ewfefrs/pi-gaze/hardware/enclosure/clamp_detail.png

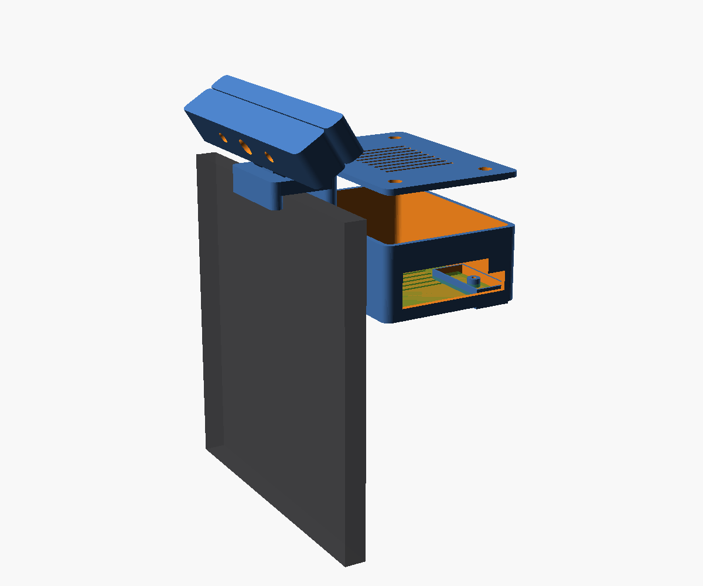
hardware/enclosure/clamp_detail.png
