ewfefrs/pi-gaze/hardware/enclosure/insp_box_in.png

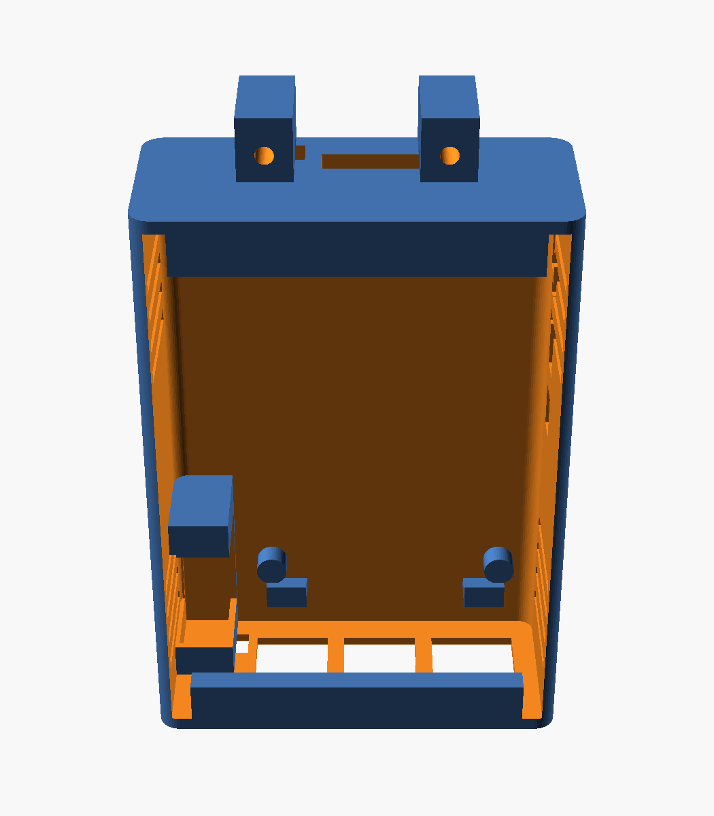
hardware/enclosure/insp_box_in.png
