ewfefrs/pi-gaze/hardware/enclosure/insp_box_xside.png

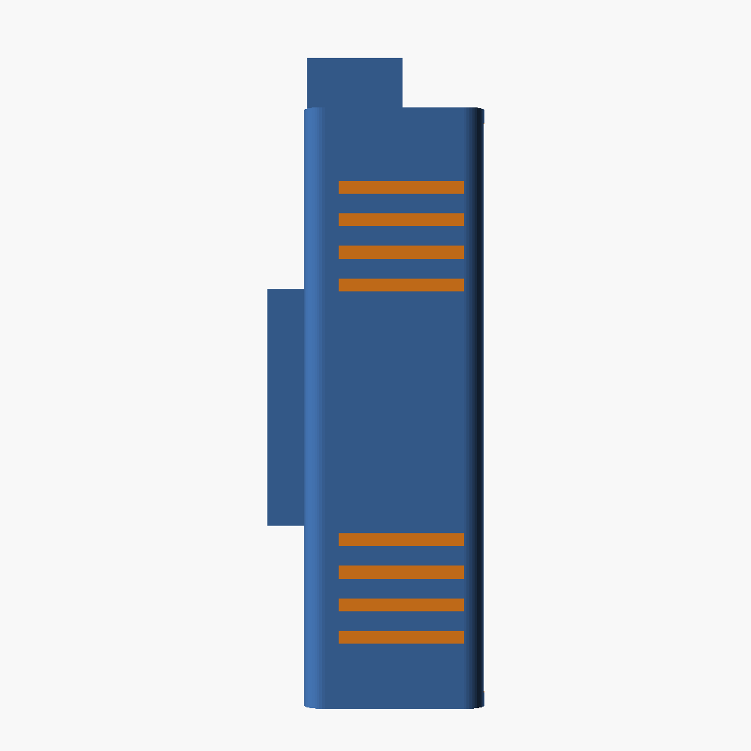
hardware/enclosure/insp_box_xside.png
