ewfefrs/pi-gaze/hardware/enclosure/insp_clamp_back.png

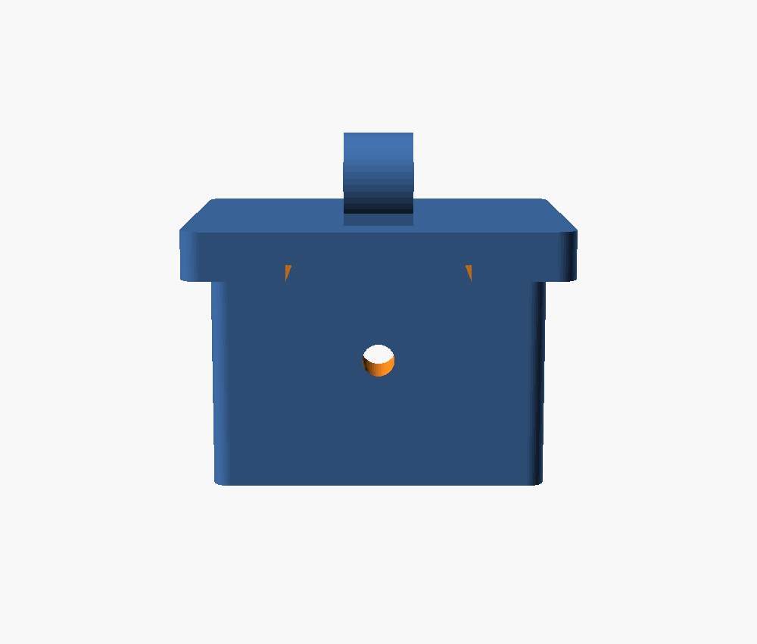
hardware/enclosure/insp_clamp_back.png
