ewfefrs/pi-gaze/hardware/enclosure/out/asm.png

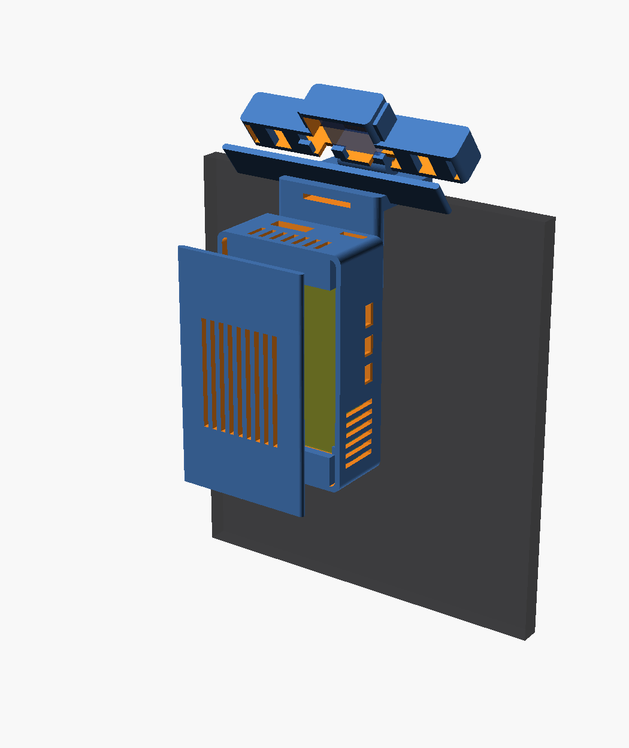
hardware/enclosure/out/asm.png
