ewfefrs/pi-gaze/hardware/enclosure/out/asm_side.png

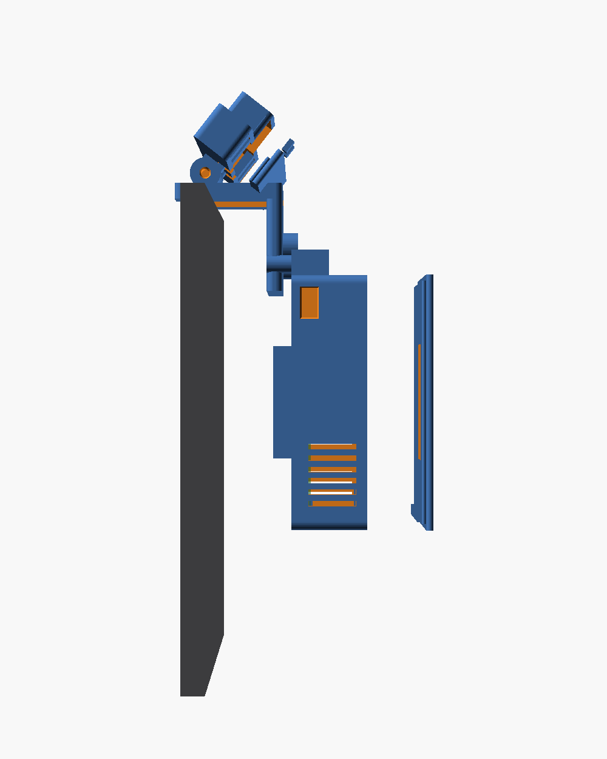
hardware/enclosure/out/asm_side.png
