ewfefrs/pi-gaze/hardware/enclosure/out/bar_back.png

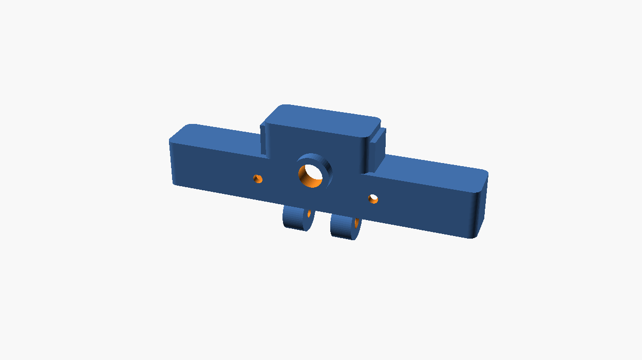
hardware/enclosure/out/bar_back.png
