ewfefrs/pi-gaze/hardware/enclosure/out/bar_iso.png

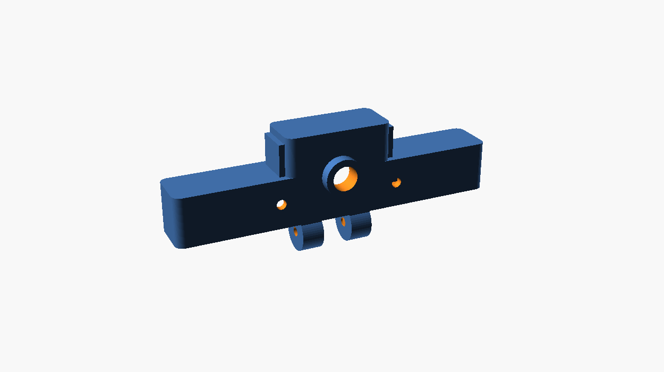
hardware/enclosure/out/bar_iso.png
