ewfefrs/pi-gaze/hardware/enclosure/out/barlid.png

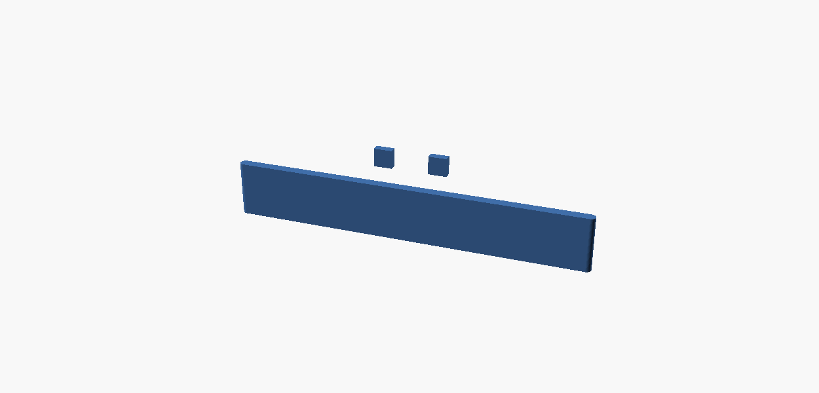
hardware/enclosure/out/barlid.png
