ewfefrs/pi-gaze/hardware/enclosure/out/box_bottom.png

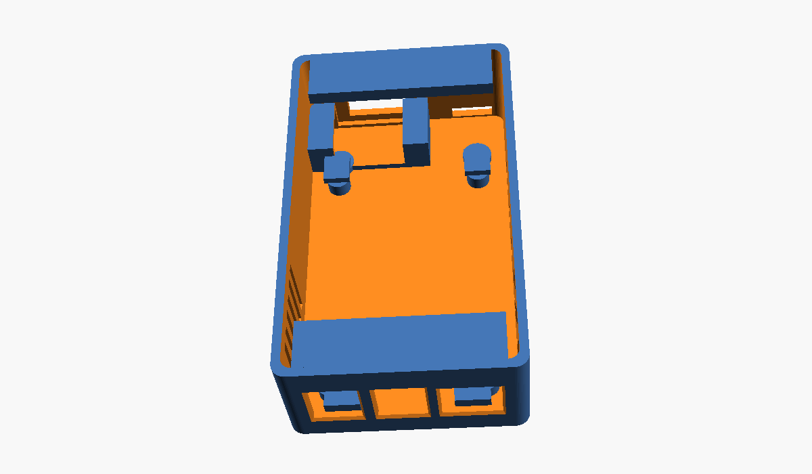
hardware/enclosure/out/box_bottom.png
