ewfefrs/pi-gaze/hardware/enclosure/out/box_ext.png

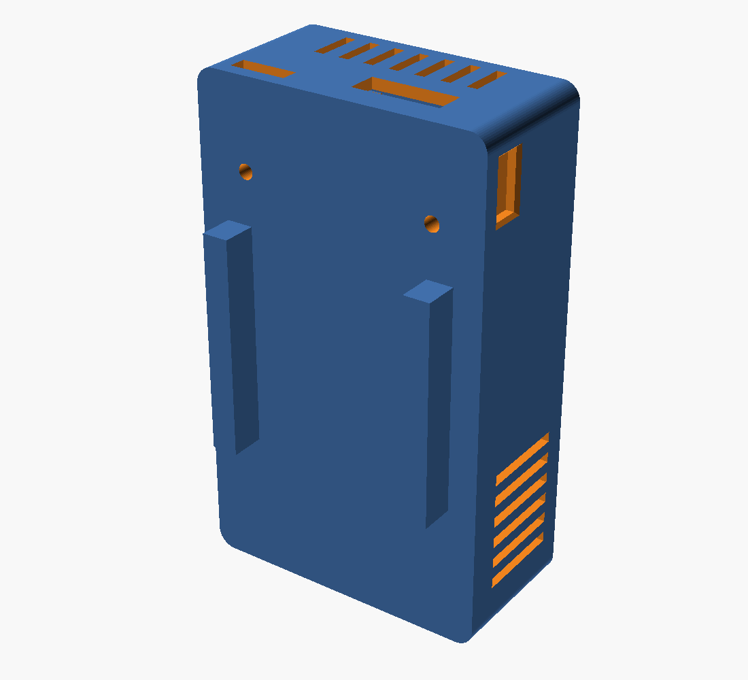
hardware/enclosure/out/box_ext.png
