ewfefrs/pi-gaze/hardware/enclosure/out/box_front.png

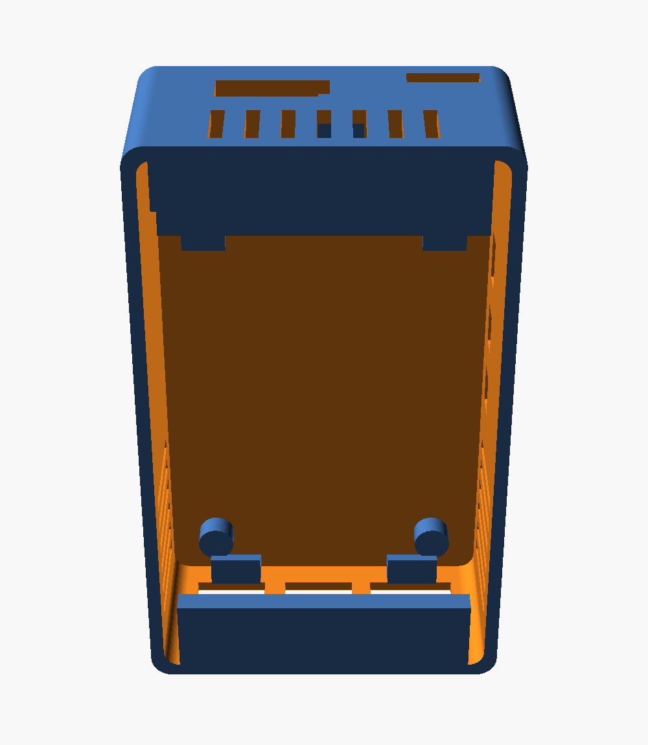
hardware/enclosure/out/box_front.png
