ewfefrs/pi-gaze/hardware/enclosure/out/box_left.png

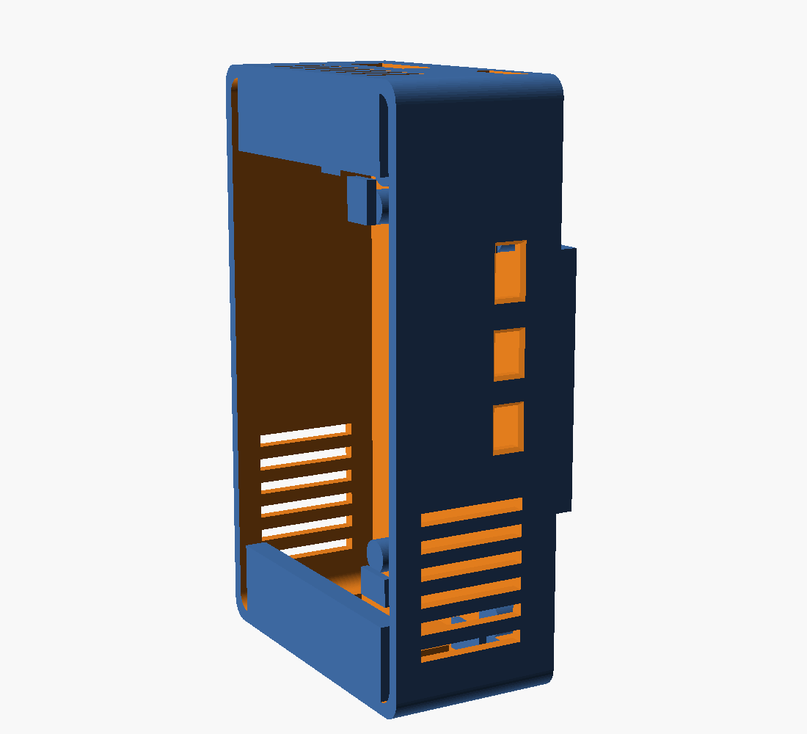
hardware/enclosure/out/box_left.png
