ewfefrs/pi-gaze/hardware/enclosure/out/box_top.png

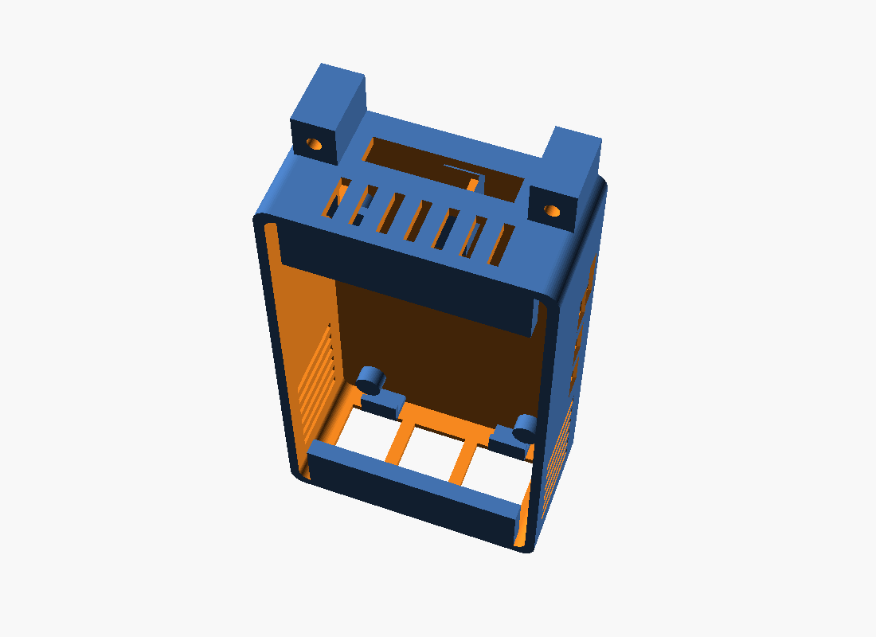
hardware/enclosure/out/box_top.png
