ewfefrs/pi-gaze/hardware/enclosure/out/chk_knob.png

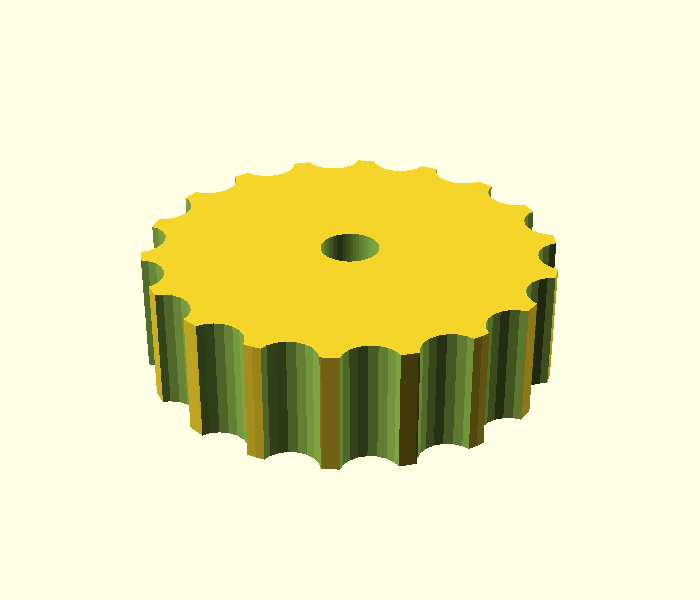
hardware/enclosure/out/chk_knob.png
