ewfefrs/pi-gaze/hardware/enclosure/out/clamp_iso.png

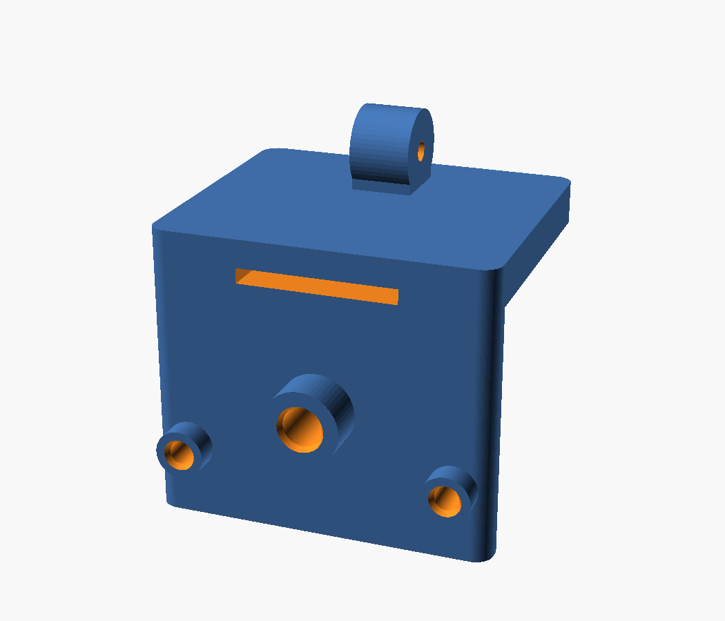
hardware/enclosure/out/clamp_iso.png
