ewfefrs/pi-gaze/hardware/enclosure/out/face_bottom.png

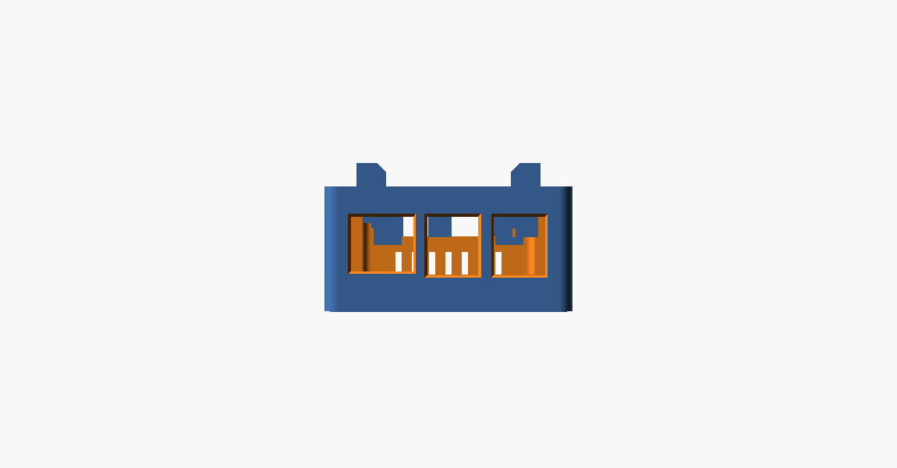
hardware/enclosure/out/face_bottom.png
