ewfefrs/pi-gaze/hardware/enclosure/out/face_left.png

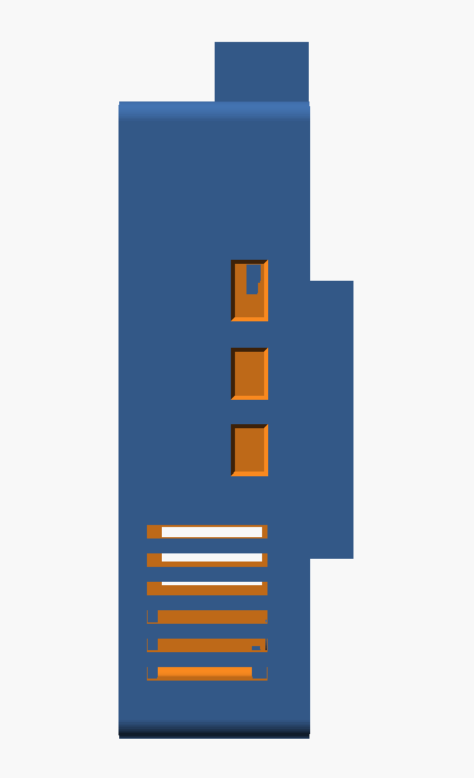
hardware/enclosure/out/face_left.png
