ewfefrs/pi-gaze/hardware/enclosure/out/face_top.png

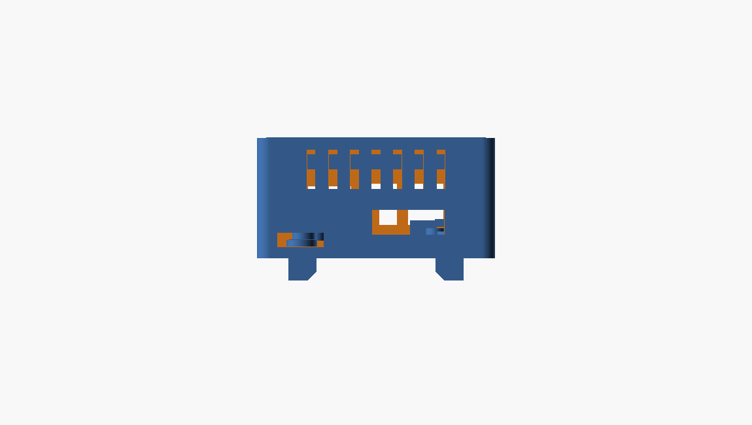
hardware/enclosure/out/face_top.png
