ewfefrs/pi-gaze/hardware/enclosure/out/final_asm2.png

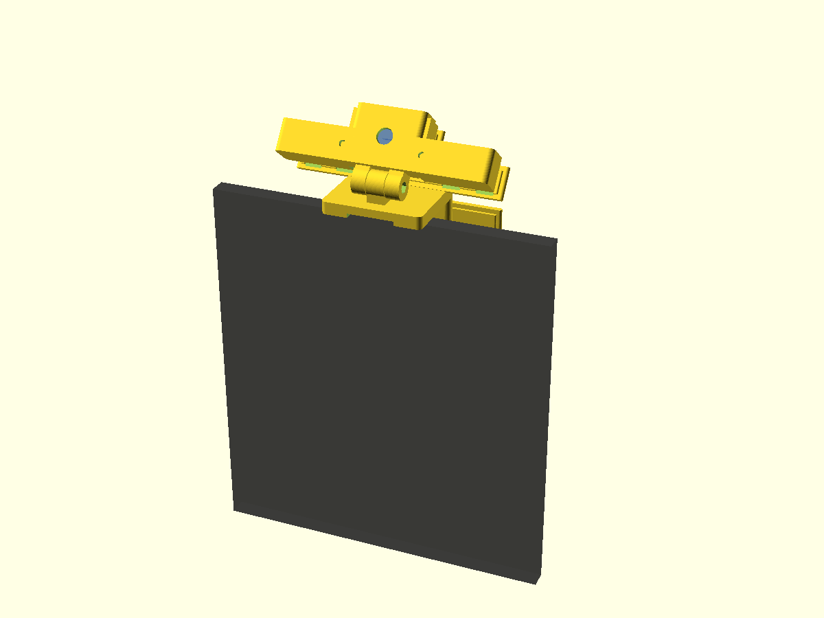
hardware/enclosure/out/final_asm2.png
