ewfefrs/pi-gaze/hardware/enclosure/out/final_barlid.png

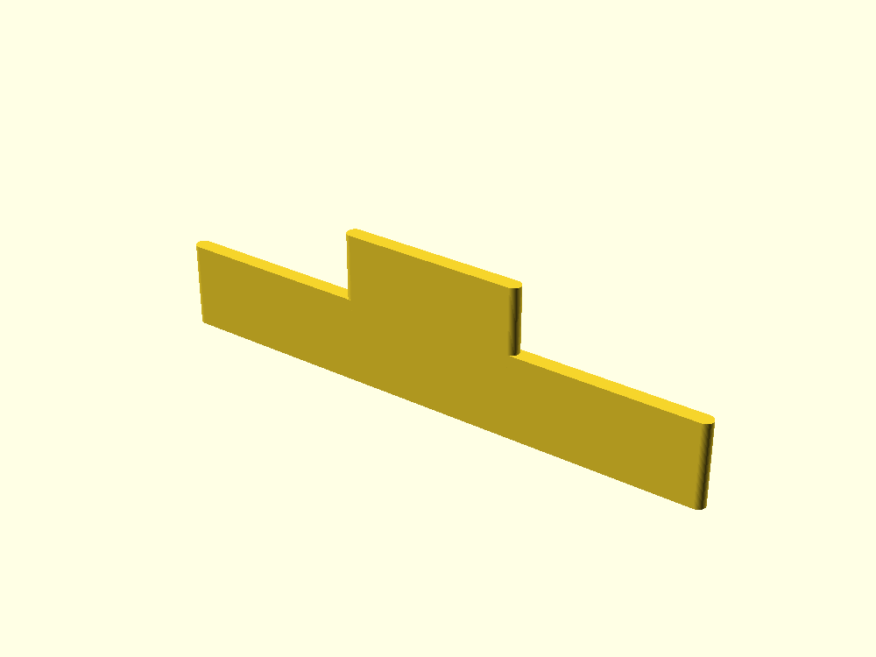
hardware/enclosure/out/final_barlid.png
