ewfefrs/pi-gaze/hardware/enclosure/out/final_box_back.png

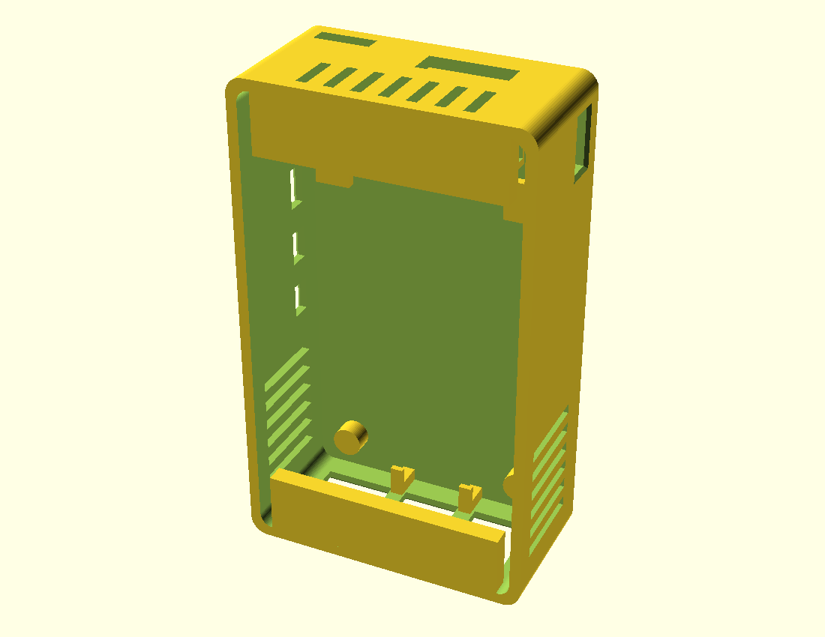
hardware/enclosure/out/final_box_back.png
