ewfefrs/pi-gaze/hardware/enclosure/out/final_box_cut.png

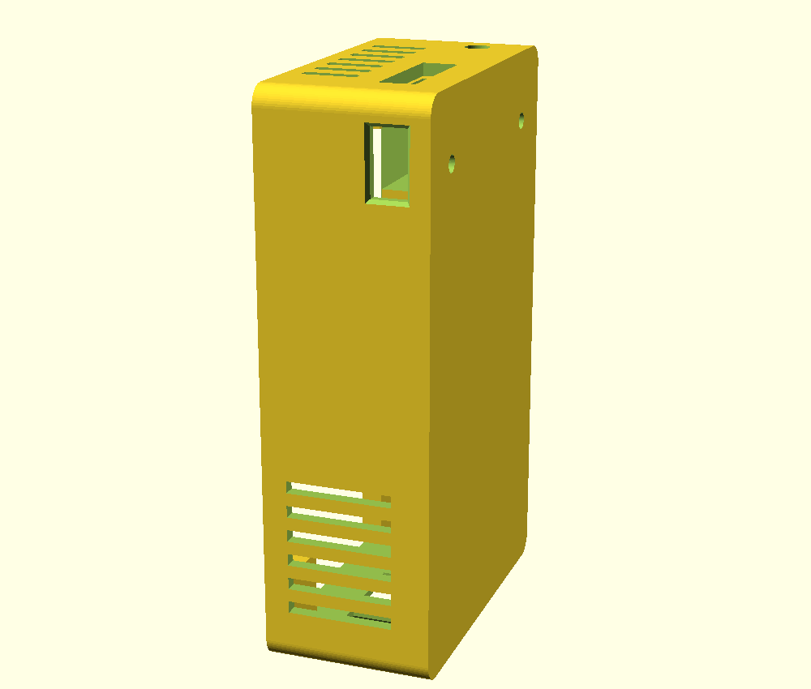
hardware/enclosure/out/final_box_cut.png
