ewfefrs/pi-gaze/hardware/enclosure/out/final_box_ports.png

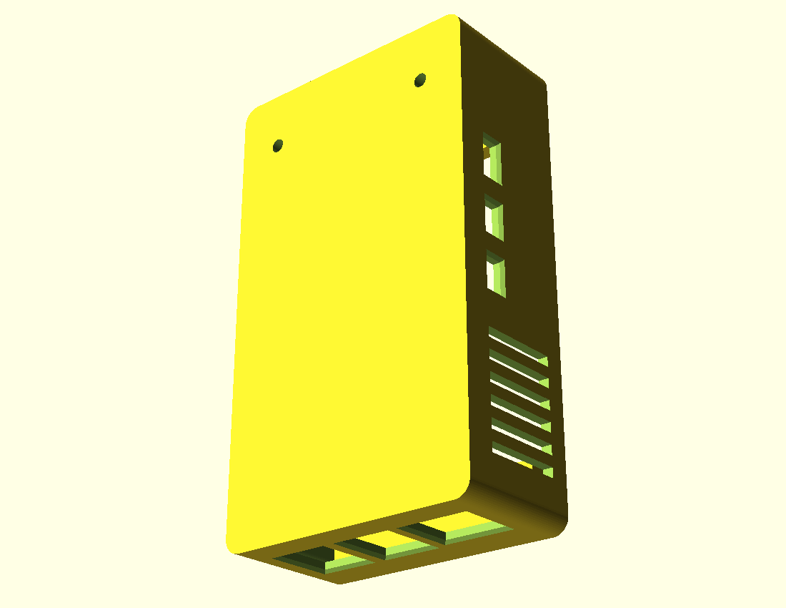
hardware/enclosure/out/final_box_ports.png
