ewfefrs/pi-gaze/hardware/enclosure/out/final_box_pwr.png

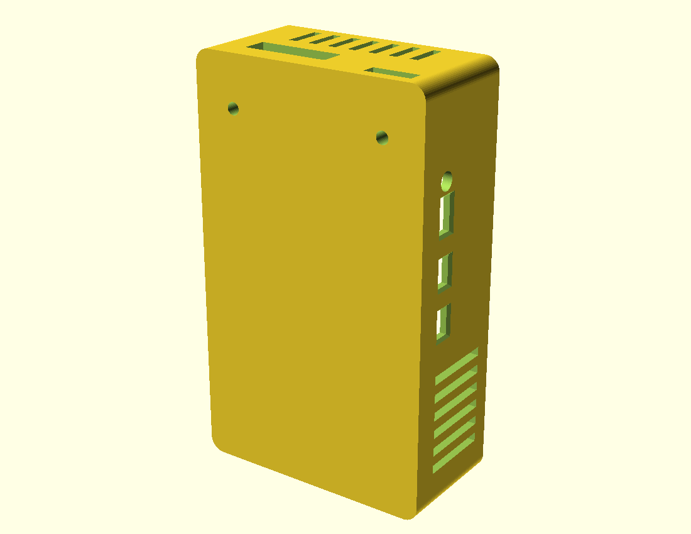
hardware/enclosure/out/final_box_pwr.png
