ewfefrs/pi-gaze/hardware/enclosure/out/final_box_top.png

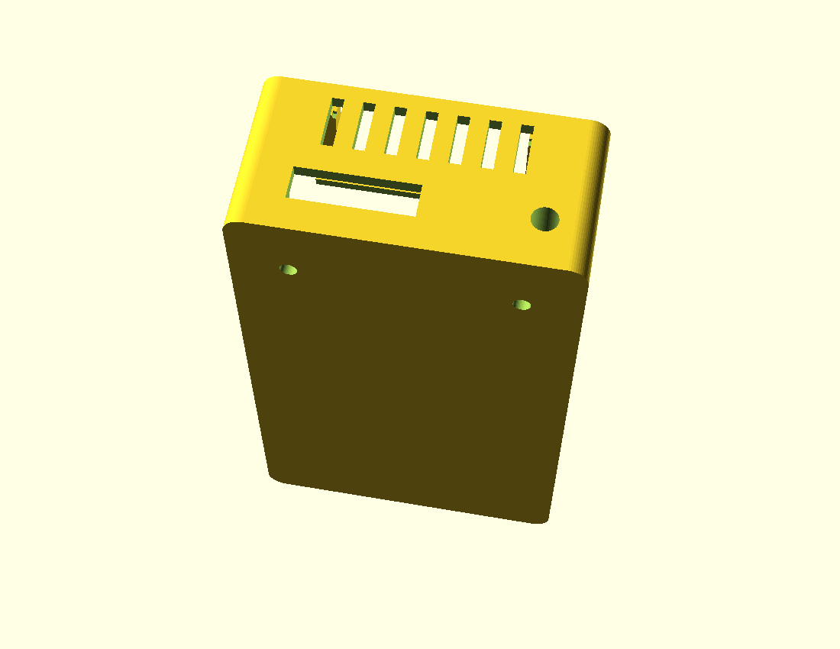
hardware/enclosure/out/final_box_top.png
