ewfefrs/pi-gaze/hardware/enclosure/out/final_clamp.png

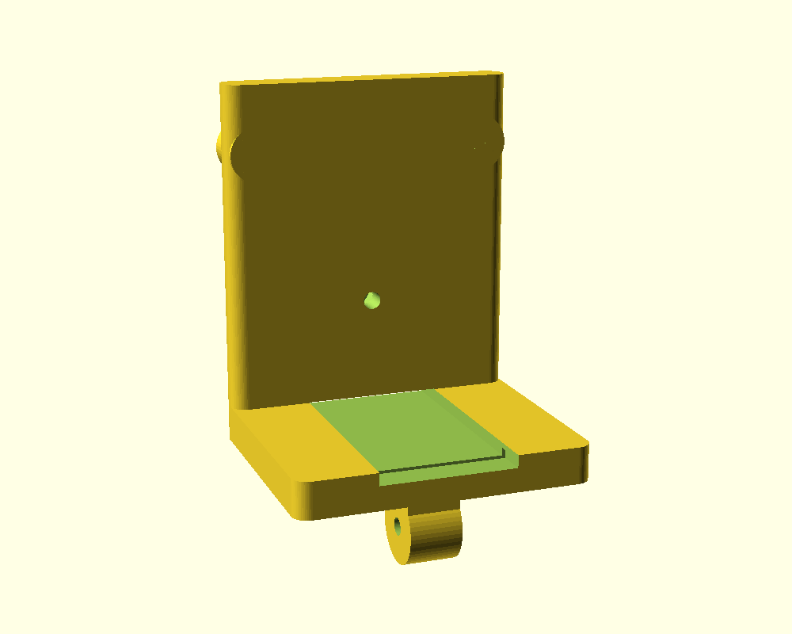
hardware/enclosure/out/final_clamp.png
