ewfefrs/pi-gaze/hardware/enclosure/out/foot_back.png

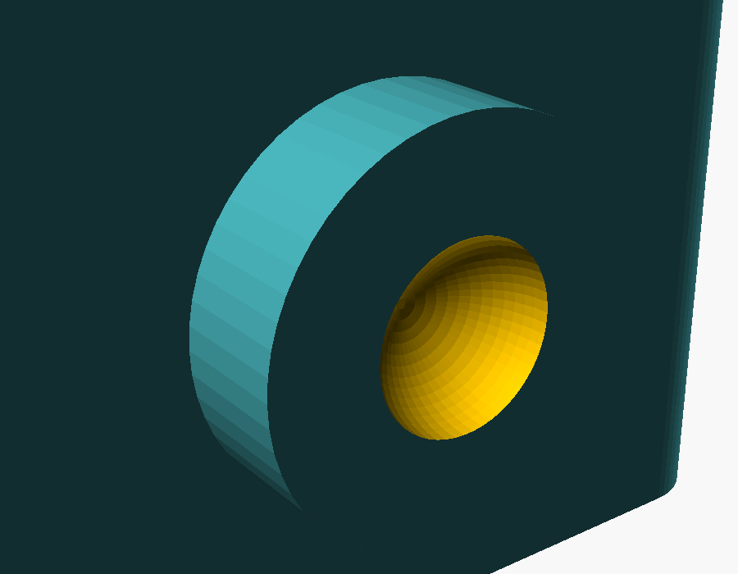
hardware/enclosure/out/foot_back.png
