ewfefrs/pi-gaze/hardware/enclosure/out/foot_fixed.png

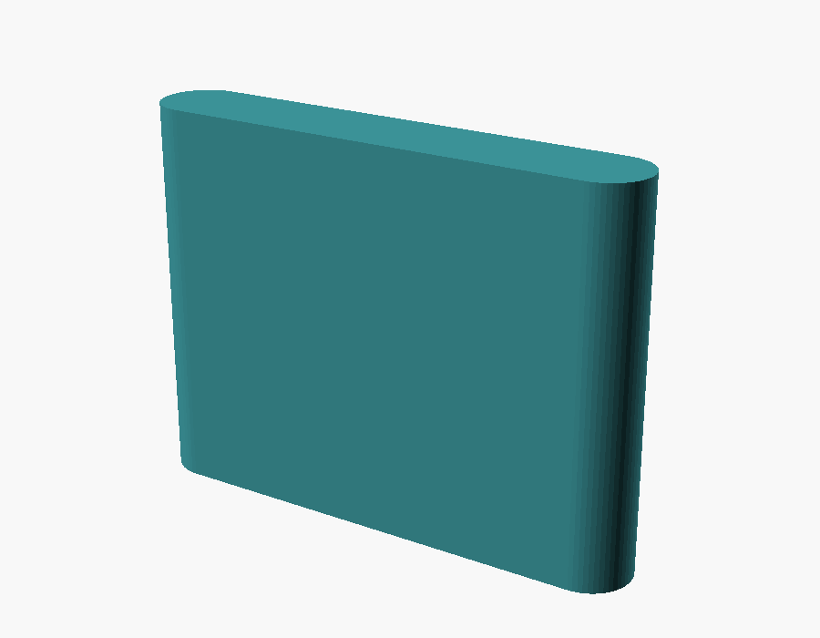
hardware/enclosure/out/foot_fixed.png
