ewfefrs/pi-gaze/hardware/enclosure/out/id_bar_lid.png

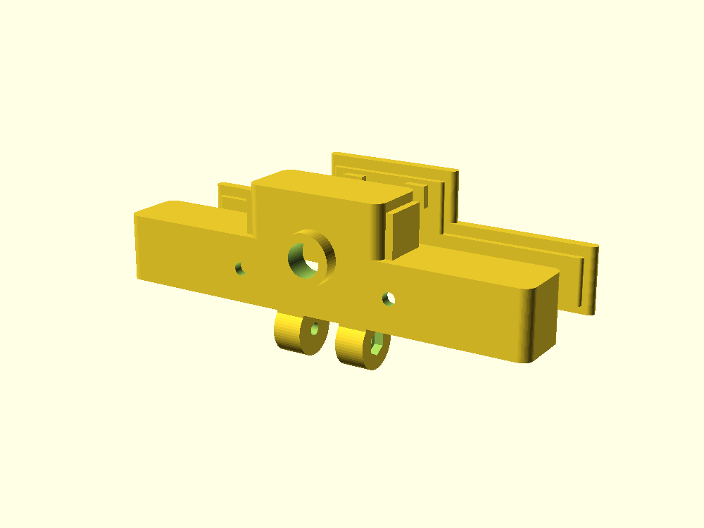
hardware/enclosure/out/id_bar_lid.png
