ewfefrs/pi-gaze/hardware/enclosure/out/id_box_front.png

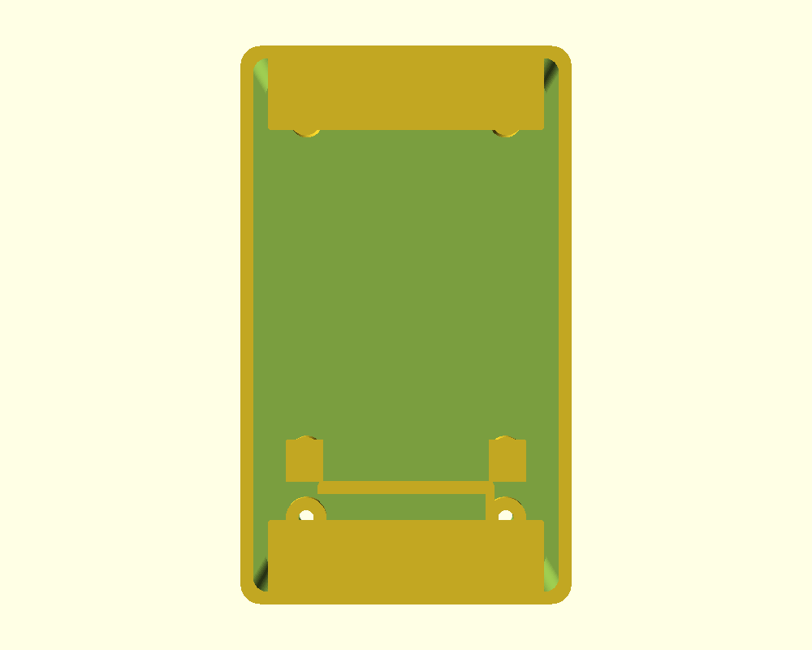
hardware/enclosure/out/id_box_front.png
