ewfefrs/pi-gaze/hardware/enclosure/out/id_clamp_under.png

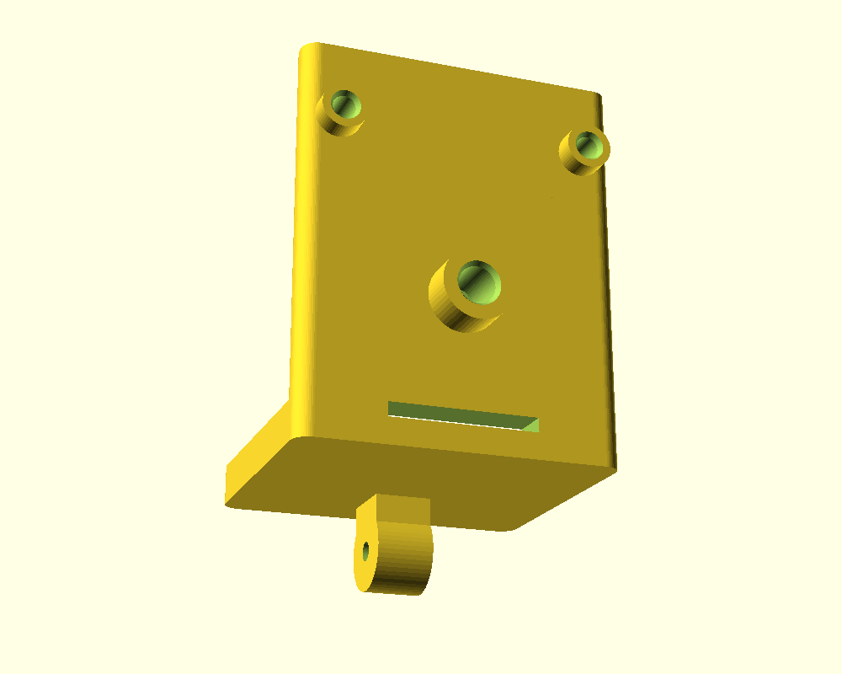
hardware/enclosure/out/id_clamp_under.png
