ewfefrs/pi-gaze/hardware/enclosure/out/insp_asm.png

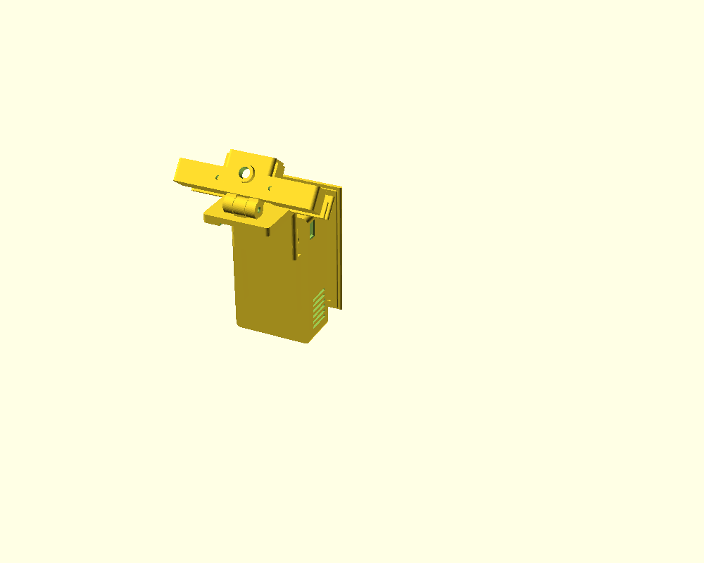
hardware/enclosure/out/insp_asm.png
