ewfefrs/pi-gaze/hardware/enclosure/out/insp_hinge.png

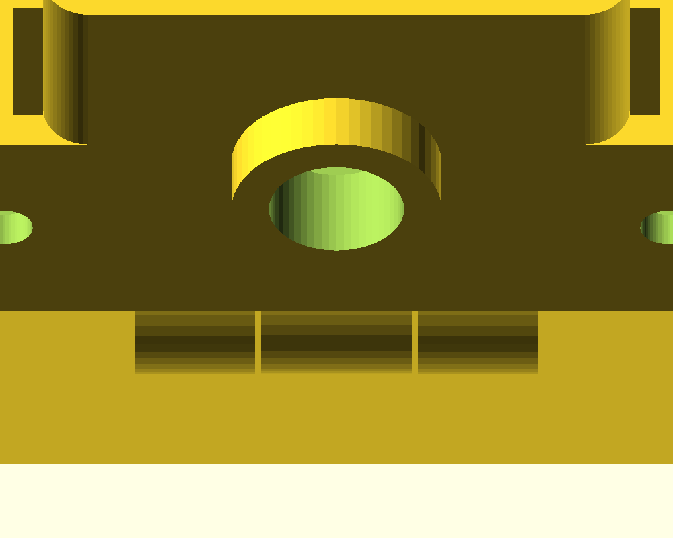
hardware/enclosure/out/insp_hinge.png
