ewfefrs/pi-gaze/hardware/enclosure/out/lid.png

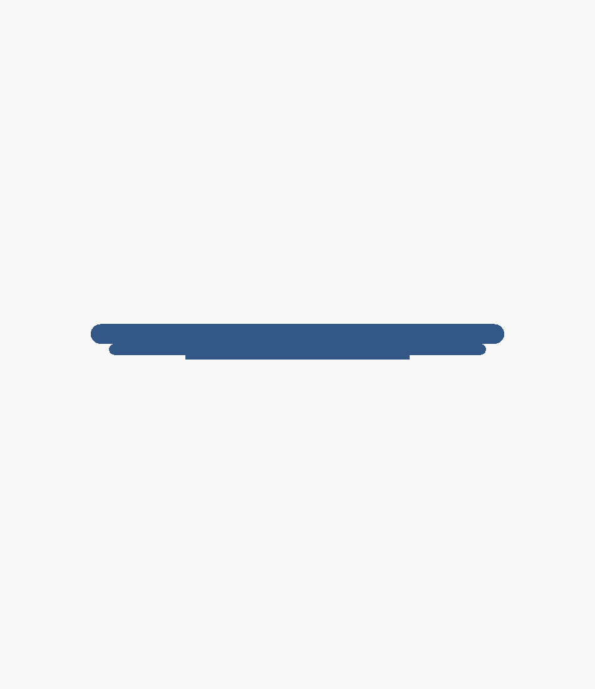
hardware/enclosure/out/lid.png
