ewfefrs/pi-gaze/hardware/enclosure/out/lid_back.png

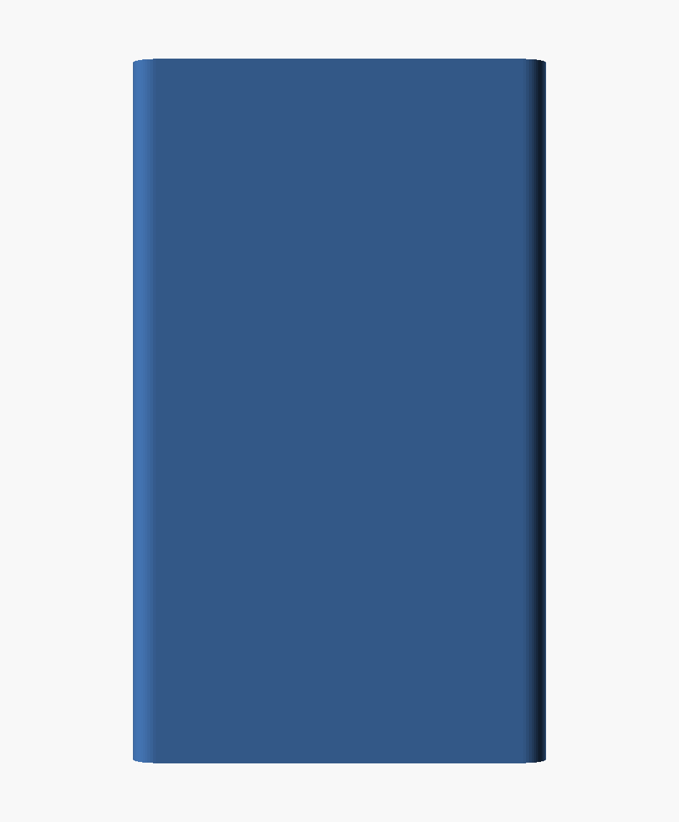
hardware/enclosure/out/lid_back.png
