ewfefrs/pi-gaze/hardware/enclosure/out/lid_iso.png

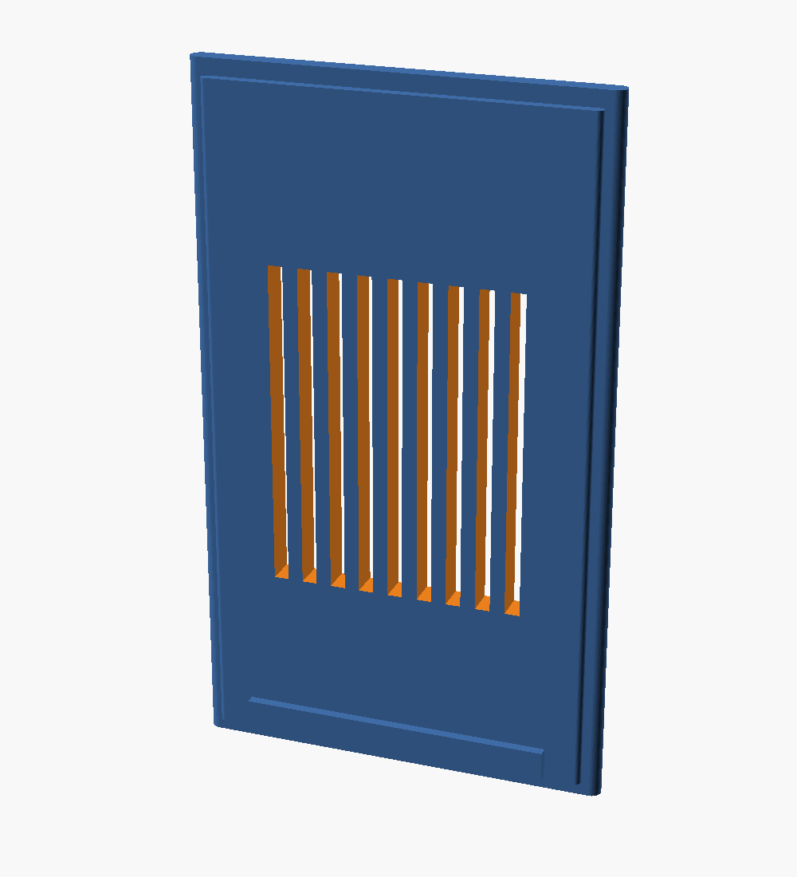
hardware/enclosure/out/lid_iso.png
