ewfefrs/pi-gaze/hardware/enclosure/out/oh_bar_front.png

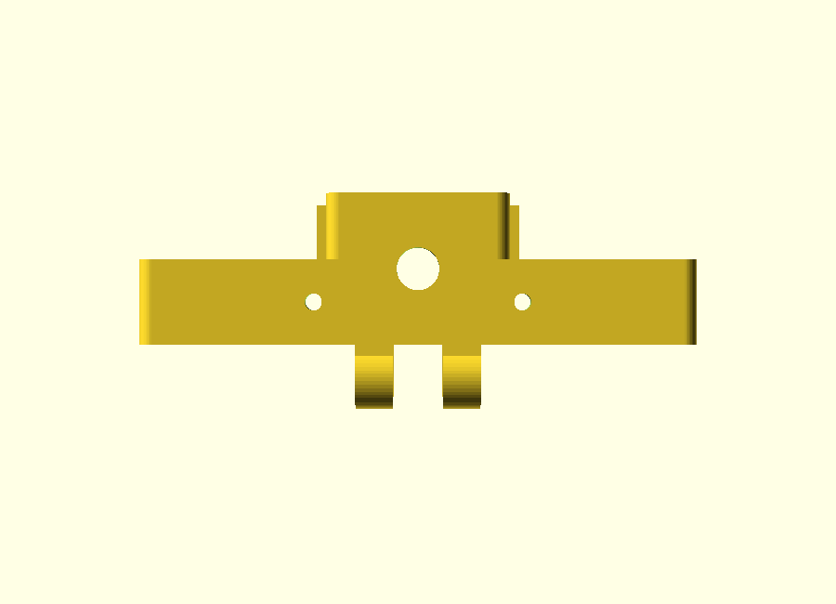
hardware/enclosure/out/oh_bar_front.png
