ewfefrs/pi-gaze/hardware/enclosure/out/oh_clamp.png

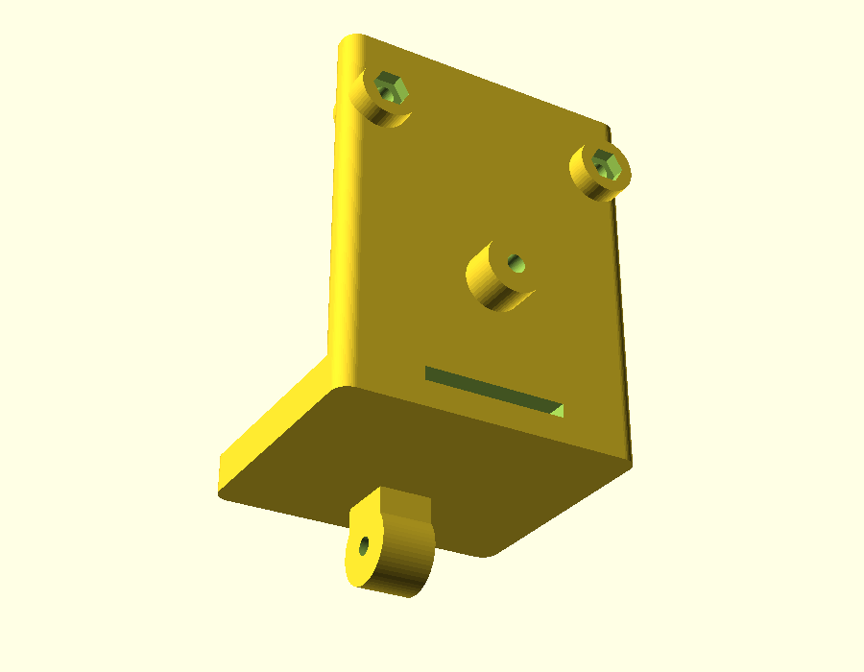
hardware/enclosure/out/oh_clamp.png
