ewfefrs/pi-gaze/hardware/enclosure/out/ov_a.png

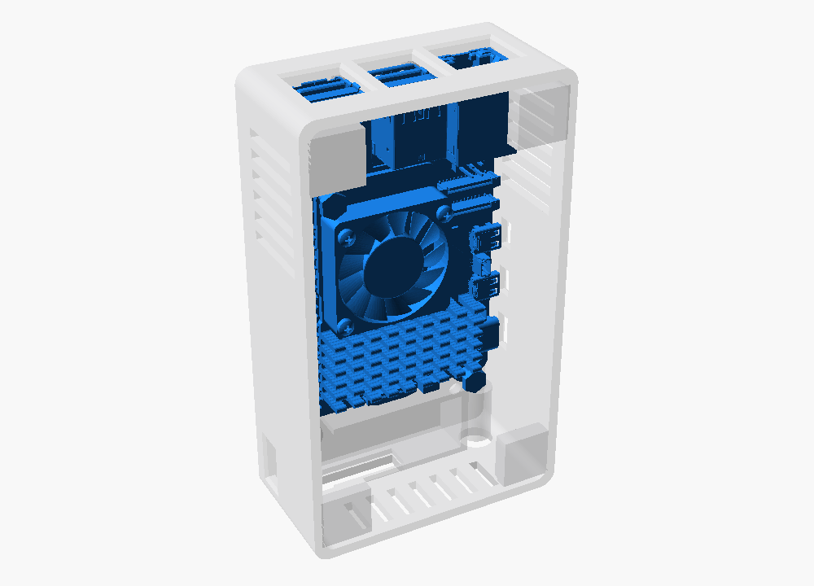
hardware/enclosure/out/ov_a.png
