ewfefrs/pi-gaze/hardware/enclosure/out/ov_side.png

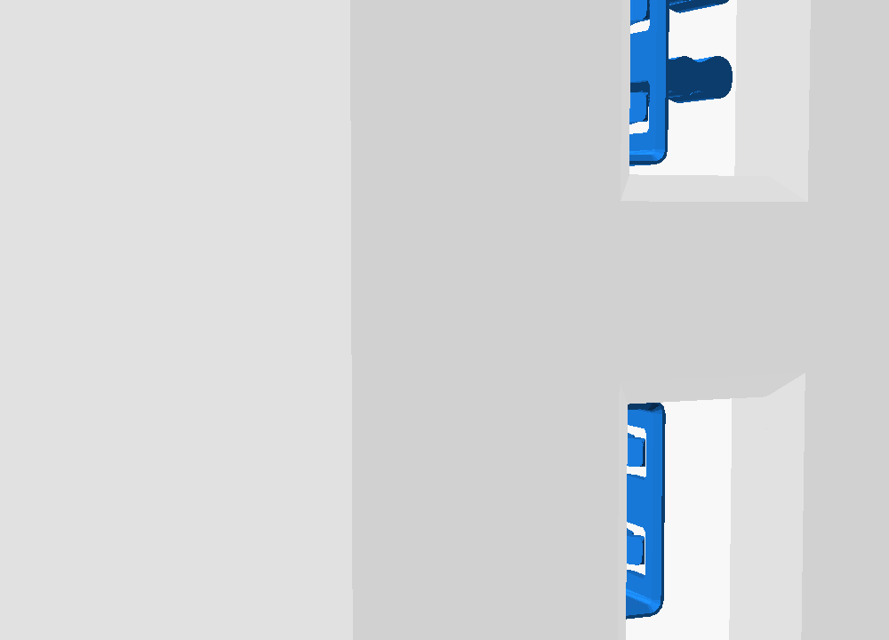
hardware/enclosure/out/ov_side.png
