ewfefrs/pi-gaze/hardware/enclosure/preview_front.png

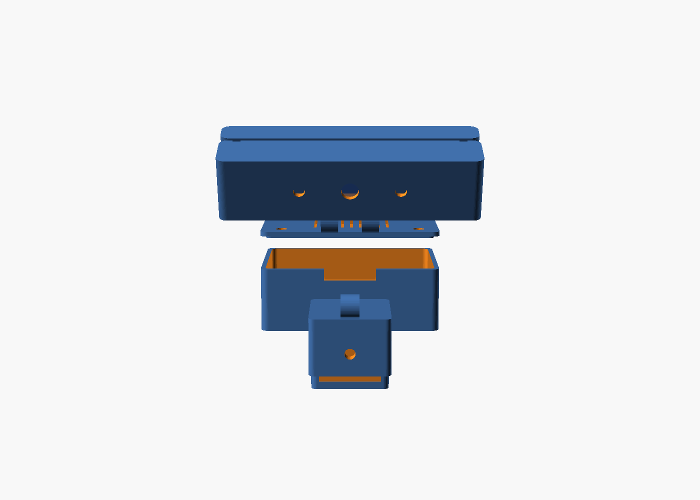
hardware/enclosure/preview_front.png
