ewfefrs/pi-gaze/hardware/enclosure/preview_iso.png

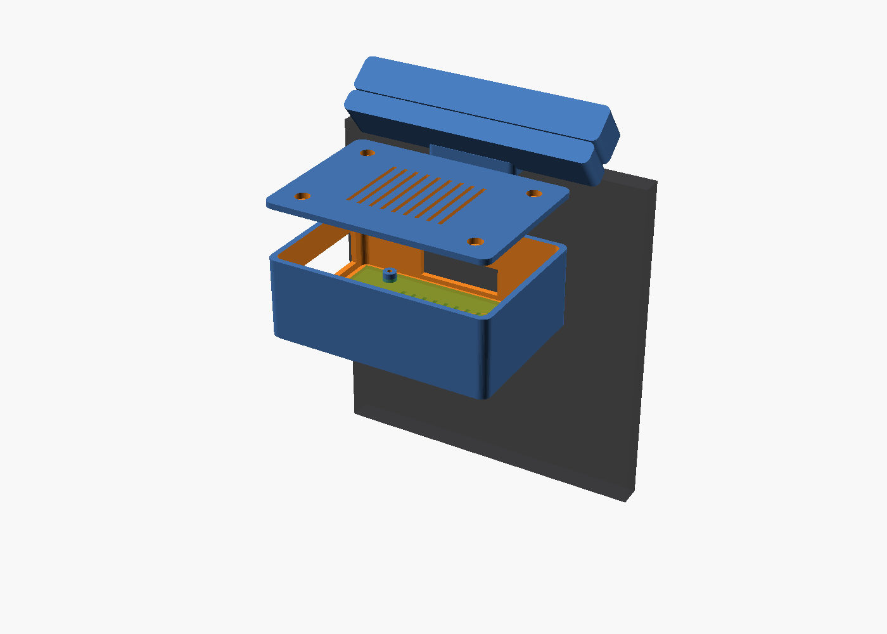
hardware/enclosure/preview_iso.png
