ewfefrs/pi-gaze/hardware/enclosure/preview_side.png

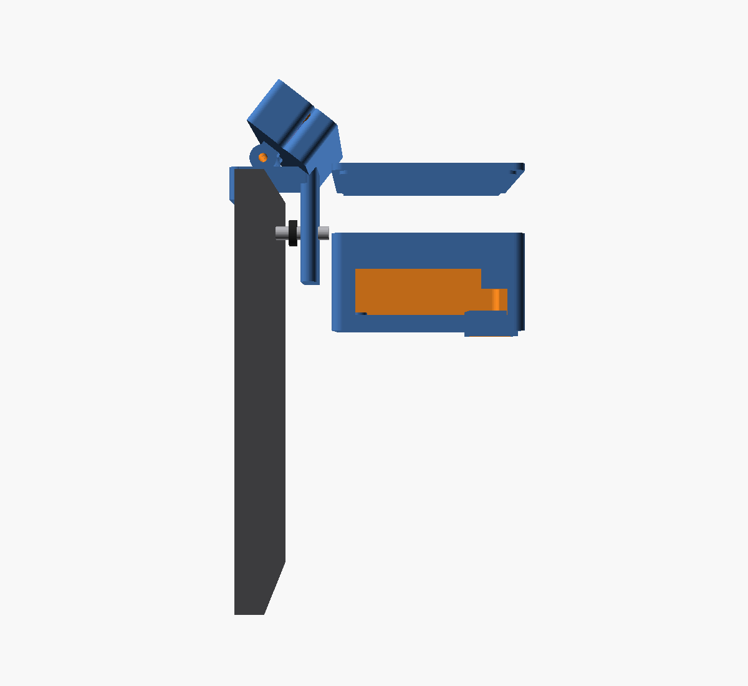
hardware/enclosure/preview_side.png
