ewfefrs/pi-gaze/hardware/enclosure/v3_box.png

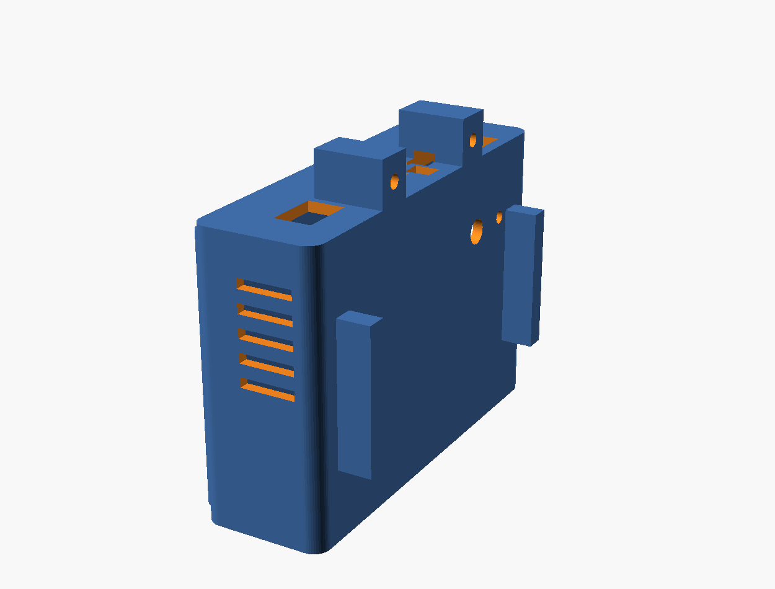
hardware/enclosure/v3_box.png
