ewfefrs/pi-gaze/hardware/enclosure/v3_ports.png

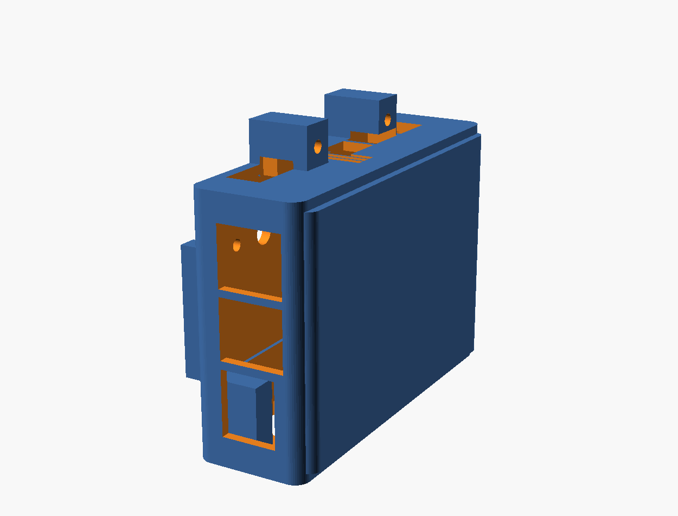
hardware/enclosure/v3_ports.png
