ewfefrs/pi-gaze/hardware/enclosure/v3_side.png

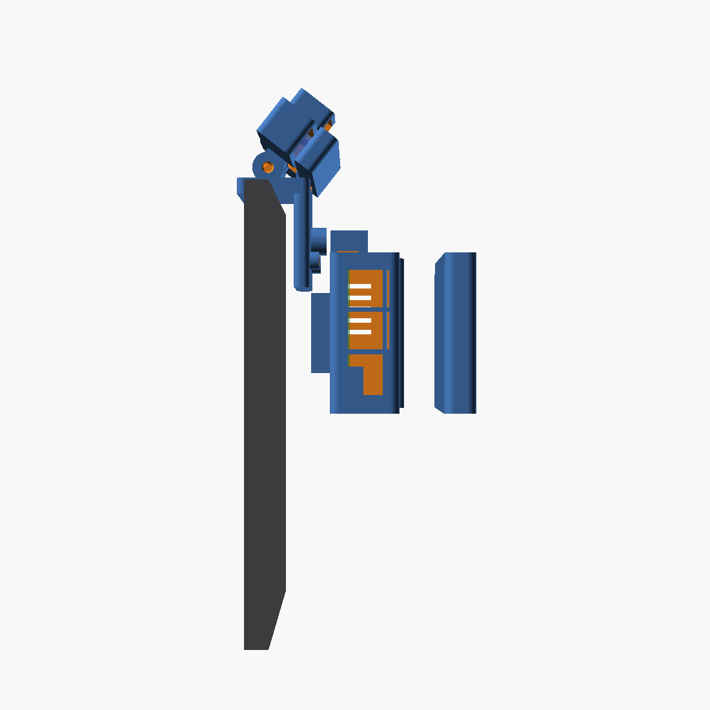
hardware/enclosure/v3_side.png
