ewfefrs/pi-gaze/hardware/enclosure/v4_box.png

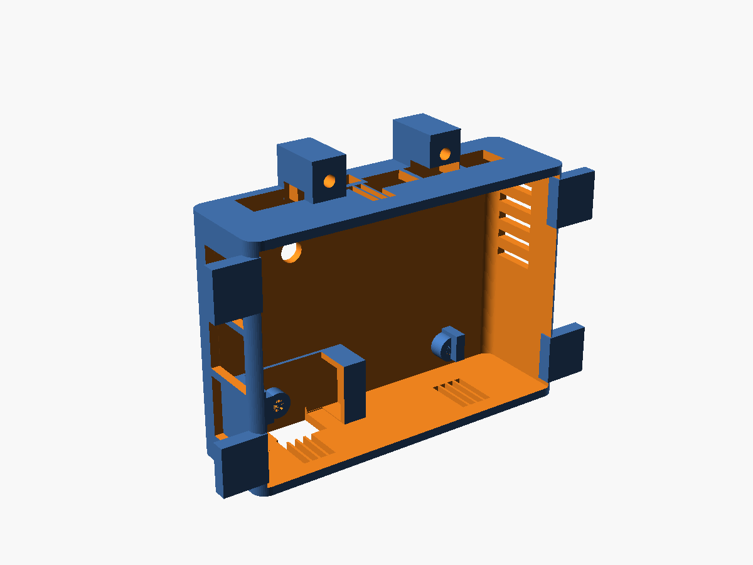
hardware/enclosure/v4_box.png
