ewfefrs/pi-gaze/hardware/enclosure/v5_asm.png

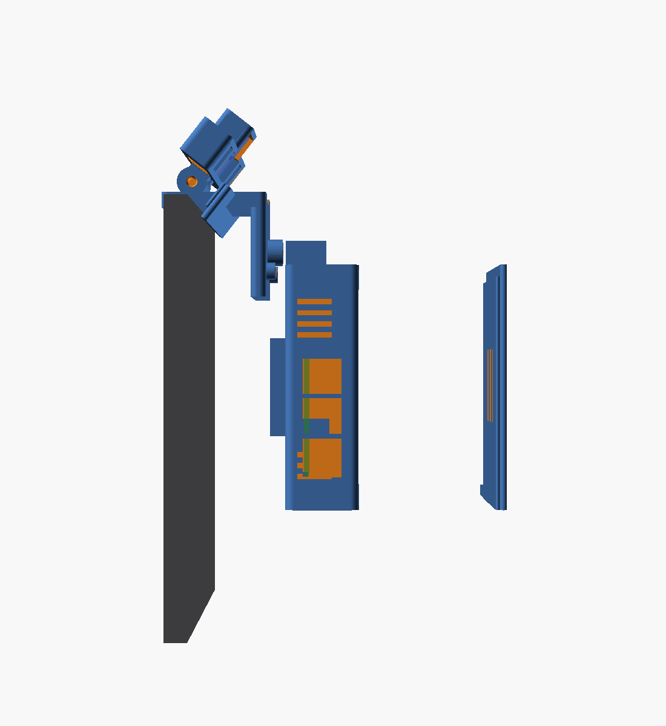
hardware/enclosure/v5_asm.png
