ewfefrs/pi-gaze/hardware/enclosure/v5_barlid.png

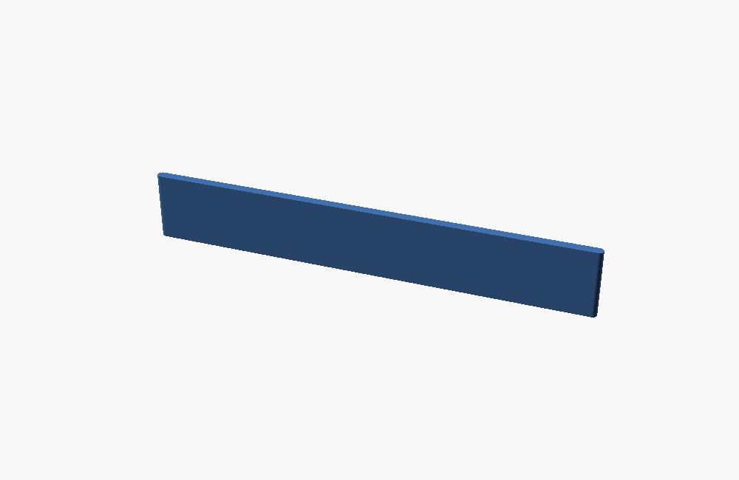
hardware/enclosure/v5_barlid.png
