ewfefrs/pi-gaze/hardware/enclosure/v5_bottom.png

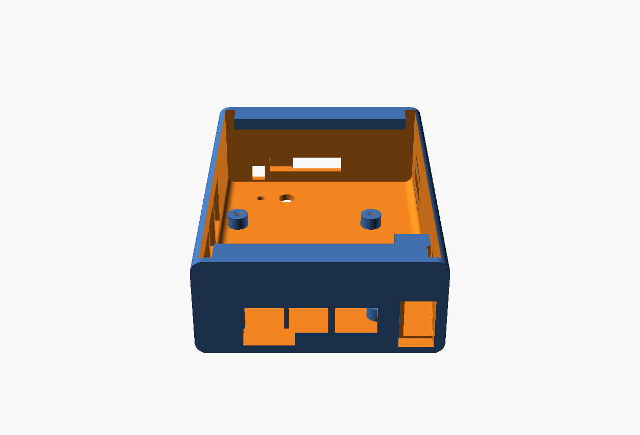
hardware/enclosure/v5_bottom.png
