ewfefrs/pi-gaze/hardware/enclosure/v5_clamp1.png

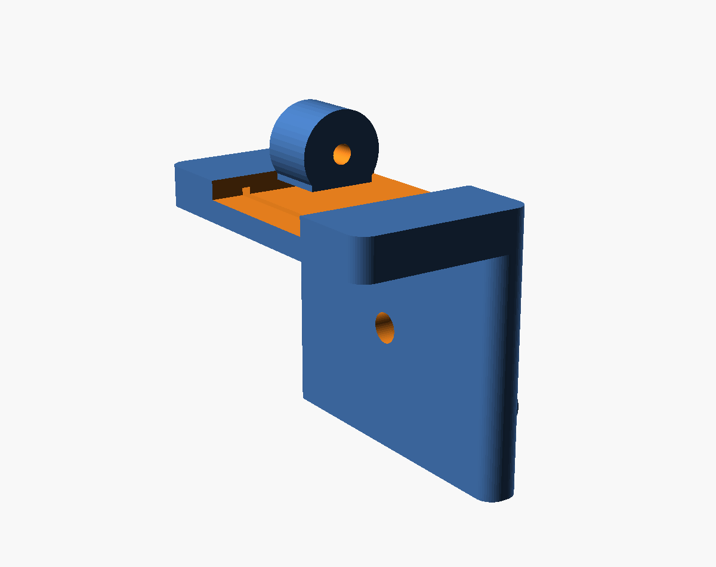
hardware/enclosure/v5_clamp1.png
