ewfefrs/pi-gaze/hardware/enclosure/v5_clamp2.png

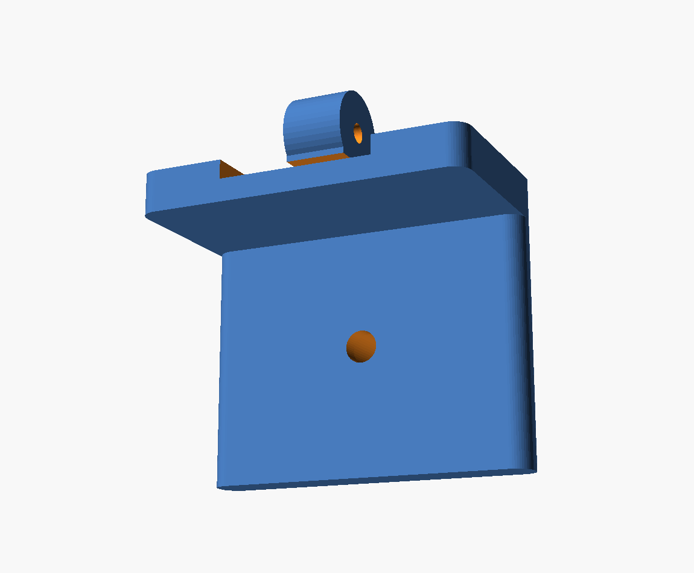
hardware/enclosure/v5_clamp2.png
