ewfefrs/pi-gaze/hardware/enclosure/v5_clamp3.png

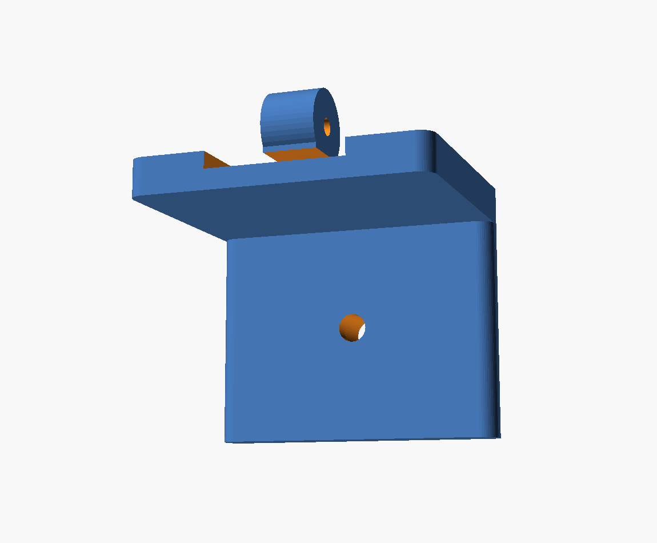
hardware/enclosure/v5_clamp3.png
