ewfefrs/pi-gaze/hardware/enclosure/v5_lid2.png

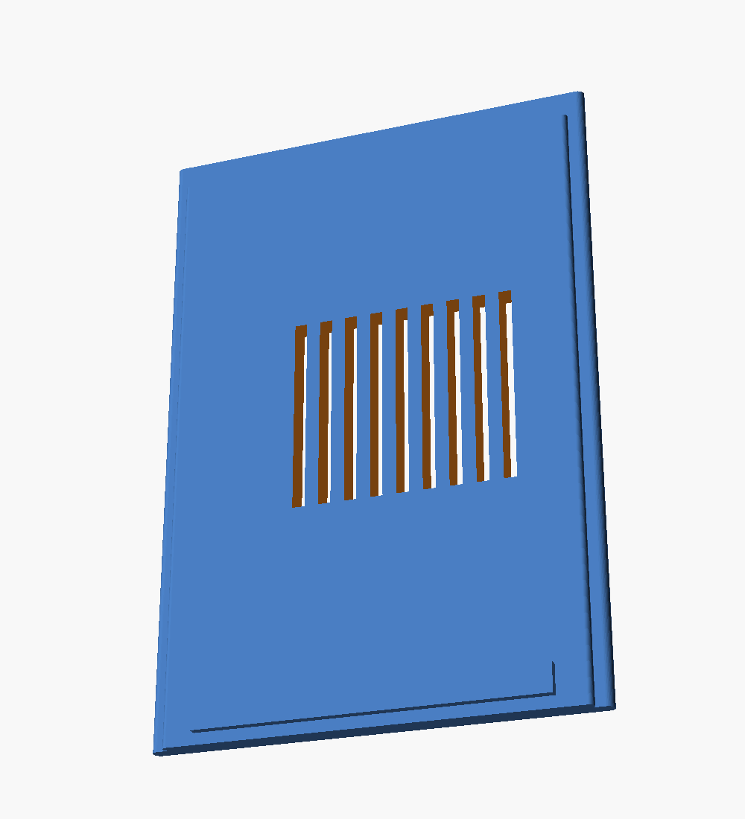
hardware/enclosure/v5_lid2.png
