ewfefrs/pi-gaze/hardware/enclosure/v5_open.png

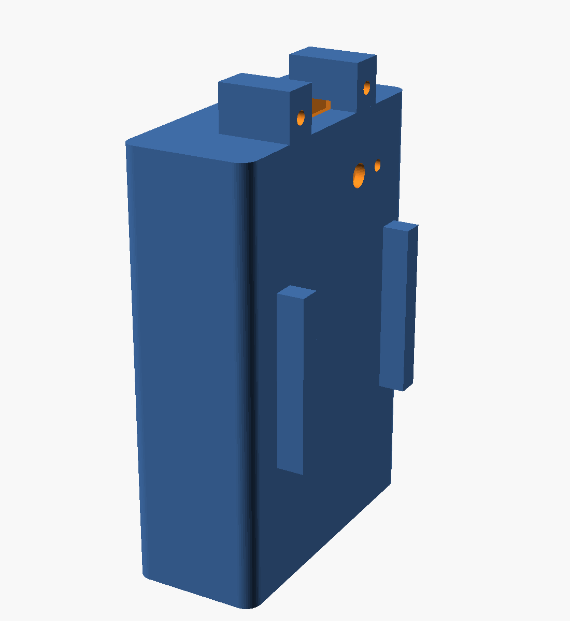
hardware/enclosure/v5_open.png
