ewfefrs/pi-gaze/hardware/enclosure/v5_side.png

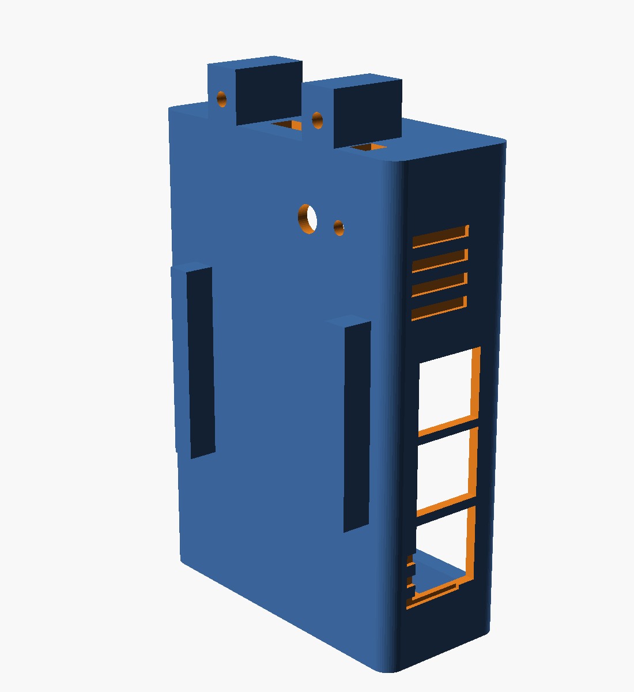
hardware/enclosure/v5_side.png
