ewfefrs/pi-gaze/hardware/enclosure/v6_asm.png

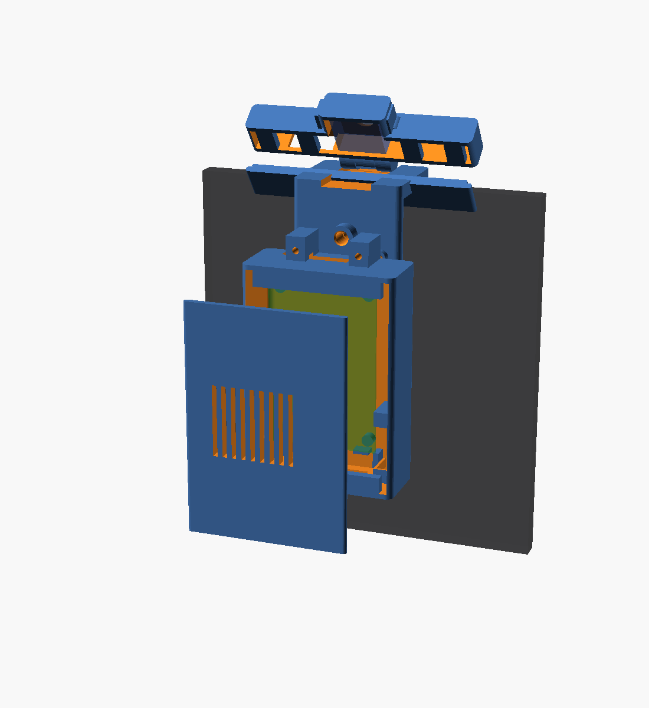
hardware/enclosure/v6_asm.png
