ewfefrs/pi-gaze/hardware/enclosure/v6_front.png

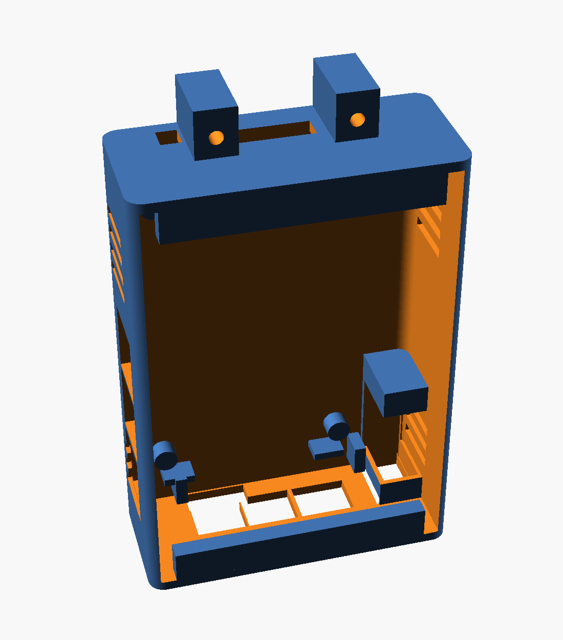
hardware/enclosure/v6_front.png
