ewfefrs/pi-gaze/hardware/enclosure/v6_lid.png

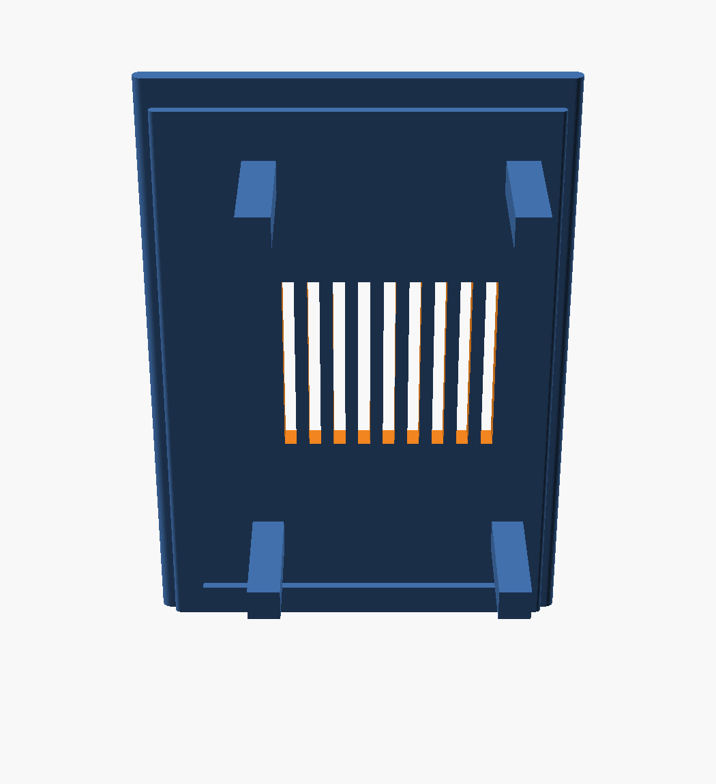
hardware/enclosure/v6_lid.png
