ewfefrs/pi-gaze/hardware/enclosure/v7_bottom.png

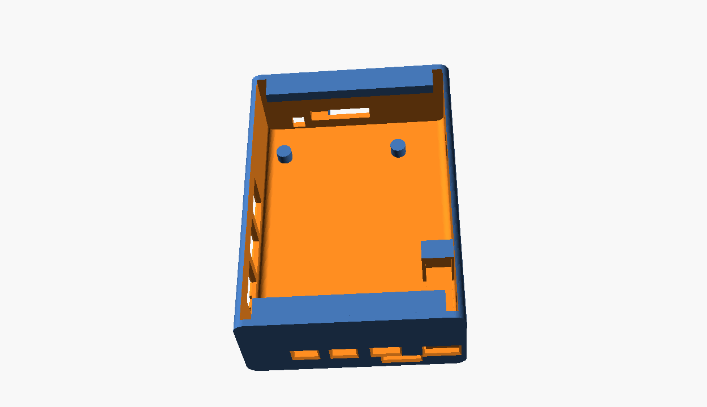
hardware/enclosure/v7_bottom.png
