ewfefrs/pi-gaze/hardware/enclosure/v7_hero.png

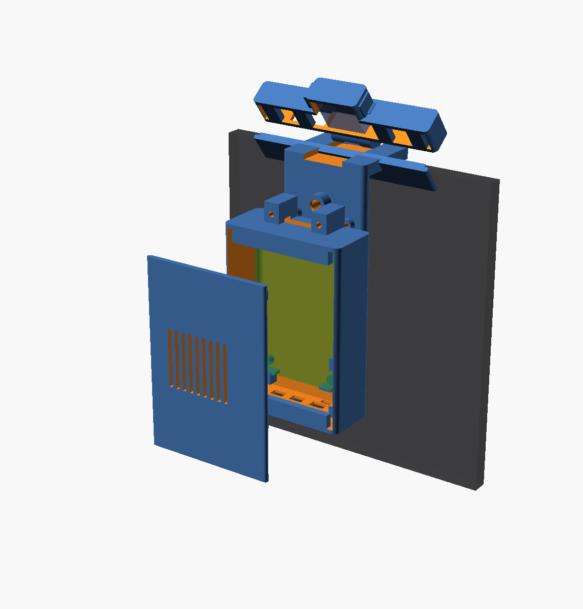
hardware/enclosure/v7_hero.png
