ewfefrs/pi-gaze/hardware/enclosure/v7_side.png

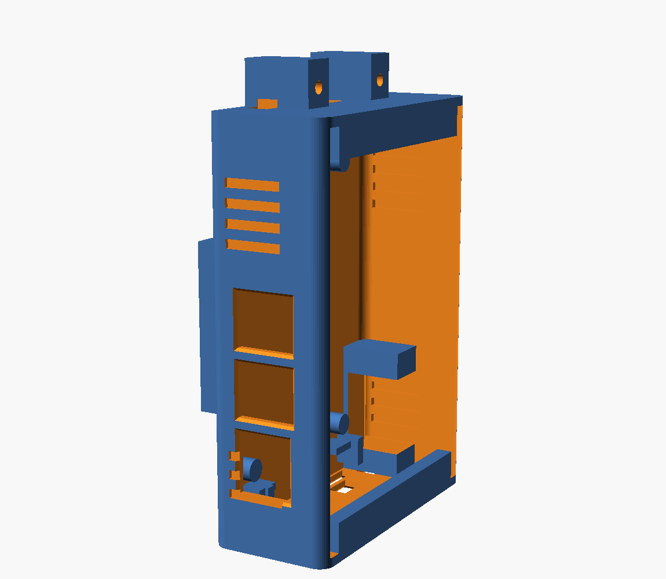
hardware/enclosure/v7_side.png
