ewfefrs/pi-gaze/hardware/enclosure/v8_bottom.png

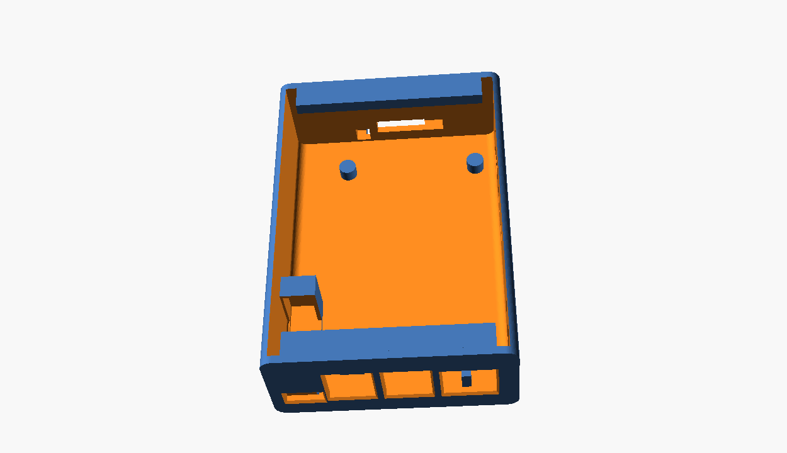
hardware/enclosure/v8_bottom.png
