ewfefrs/pi-gaze/hardware/enclosure/v8_clamp.png

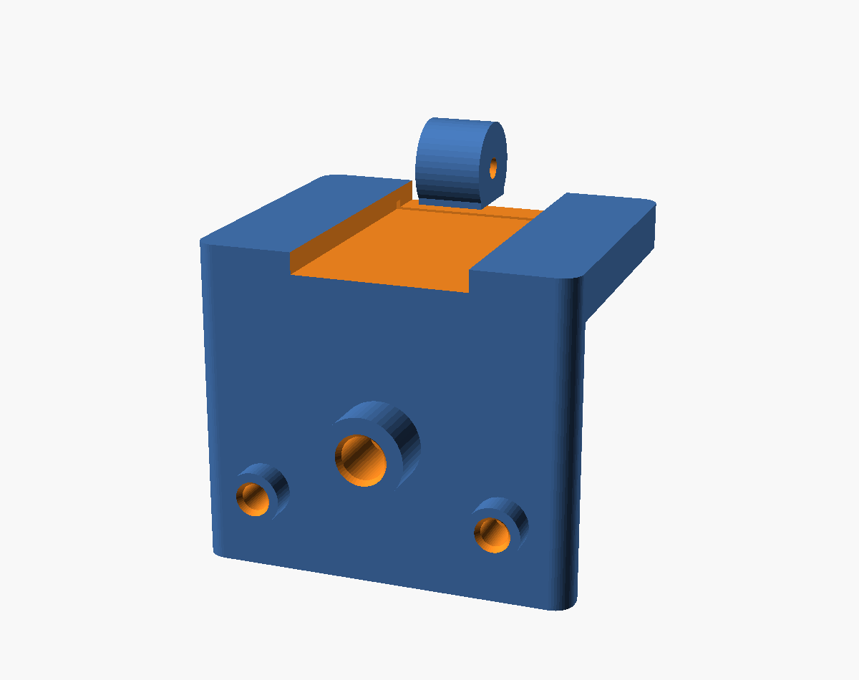
hardware/enclosure/v8_clamp.png
