ewfefrs/pi-gaze/hardware/enclosure/v8_left.png

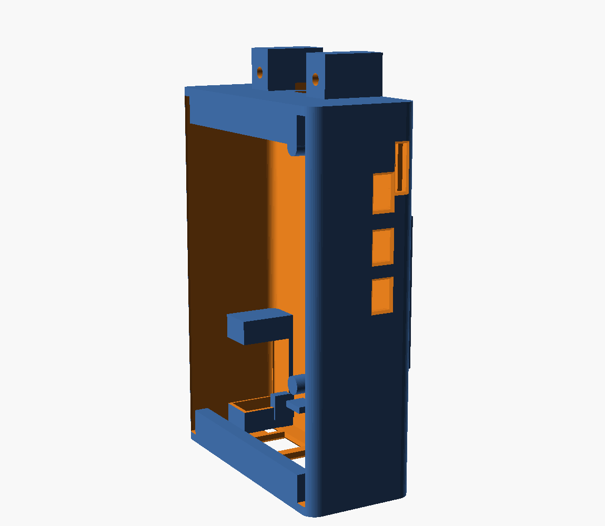
hardware/enclosure/v8_left.png
