ewfefrs/pi-gaze/hardware/enclosure/v8_lid.png

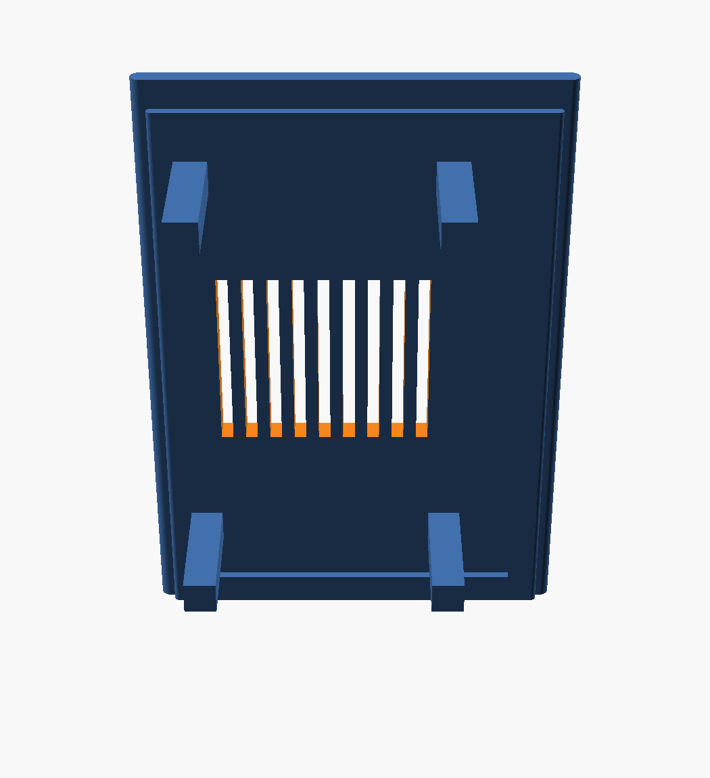
hardware/enclosure/v8_lid.png
