ewfefrs/pi-gaze/hardware/enclosure/v9_lid.png

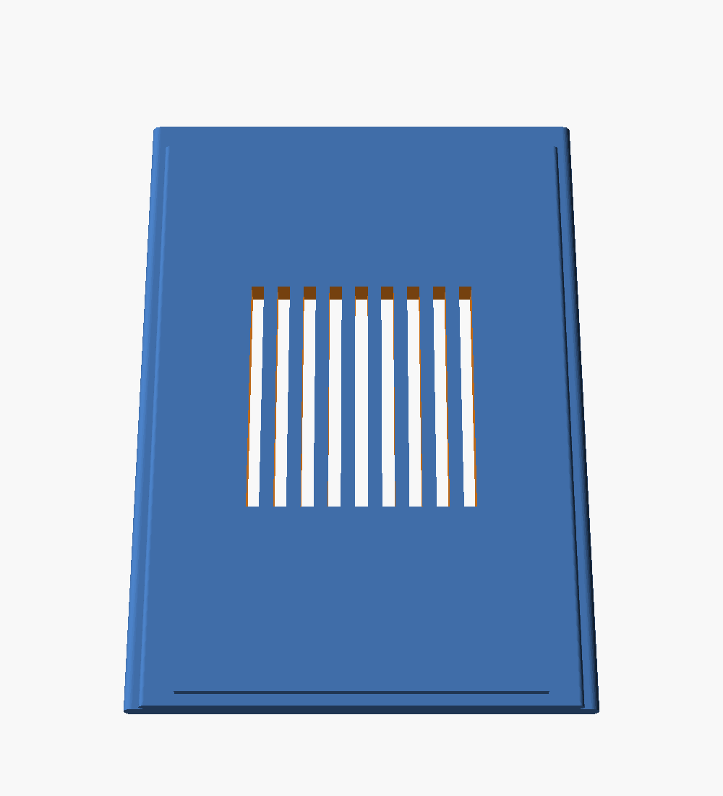
hardware/enclosure/v9_lid.png
