ewfefrs/pi-gaze/hardware/enclosure/v10_ext.png

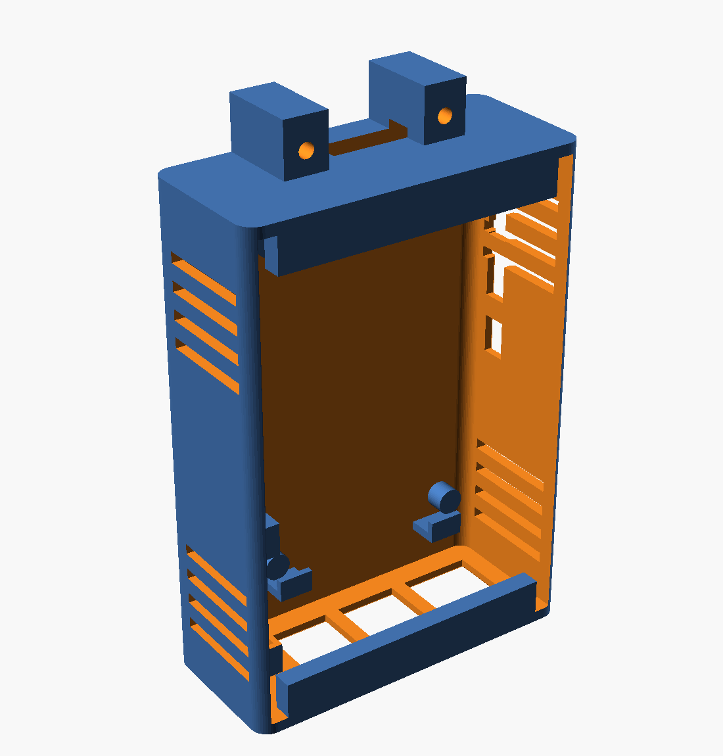
hardware/enclosure/v10_ext.png
