ewfefrs/pi-gaze/hardware/renders/cover_pigaze_preview.png

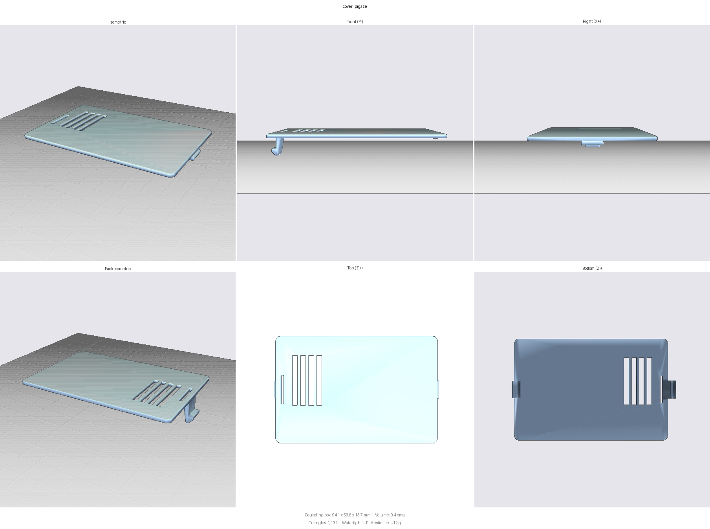
hardware/renders/cover_pigaze_preview.png
