ewfefrs/pi-gaze/hardware/renders/pigaze_bar_lid_preview.png

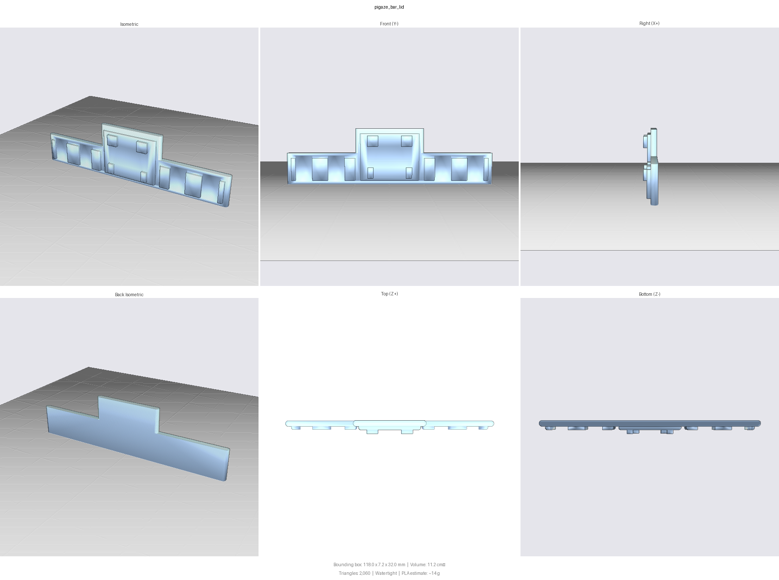
hardware/renders/pigaze_bar_lid_preview.png
