ewfefrs/pi-gaze/hardware/renders/pigaze_knob_preview.png

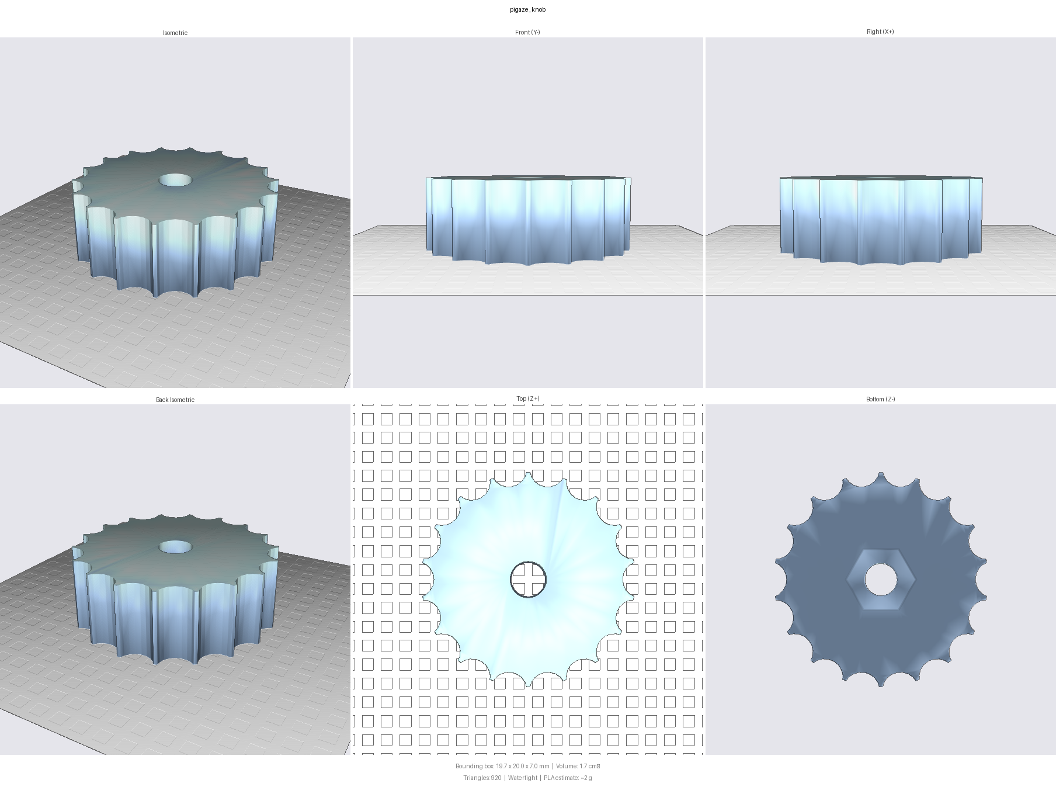
hardware/renders/pigaze_knob_preview.png
