ewfefrs/pi-gaze/hardware/enclosure/out/pose/pose_knob.stl

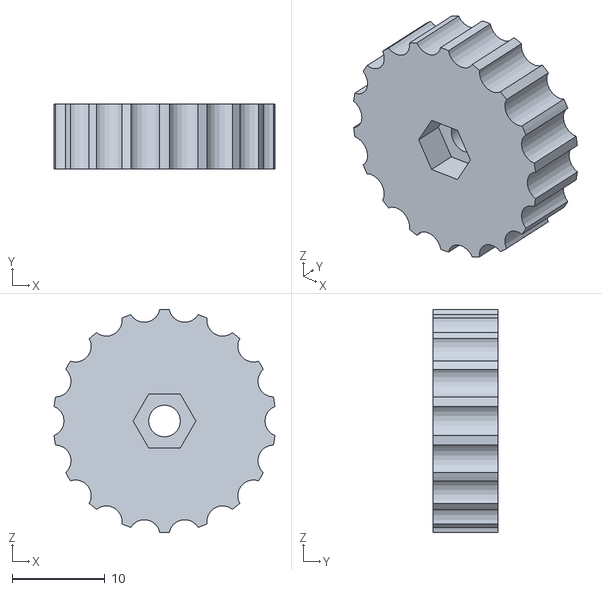
[picture p93: CAD file, 2026-10-01]
hardware/enclosure/out/pose/pose_knob.stl
23.8 x 7.00 x 24.0
