ewfefrs/pi-gaze/hardware/enclosure/stl/pigaze_clamp.stl

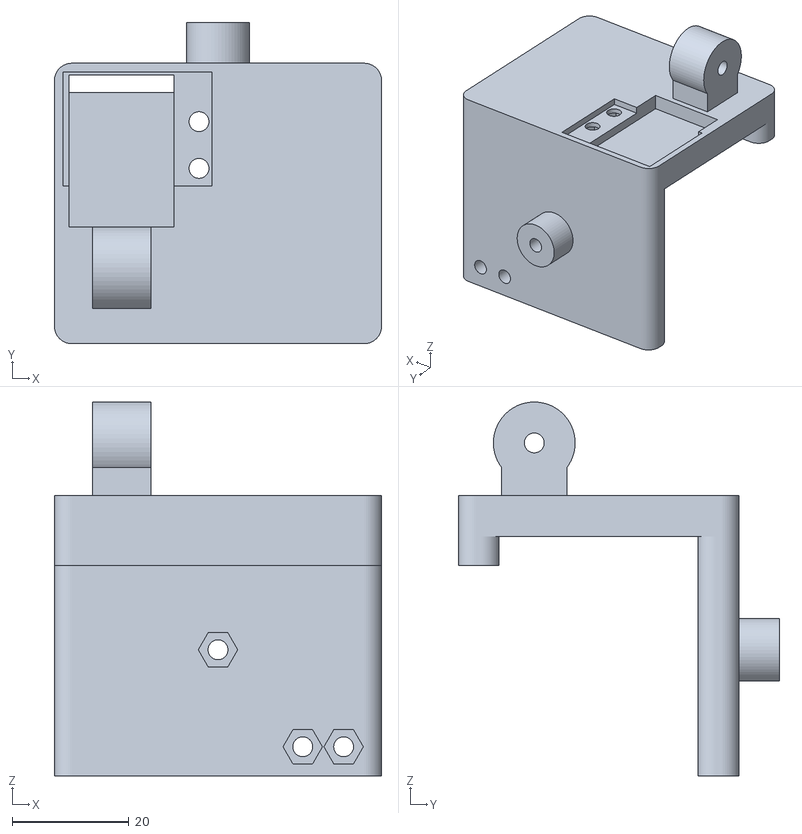
[picture p94: CAD file, 2026-10-01]
hardware/enclosure/stl/pigaze_clamp.stl
56.0 x 55.0 x 64.0
