ewfefrs/pi-gaze/hardware/mount/_tmp/case_add.stl

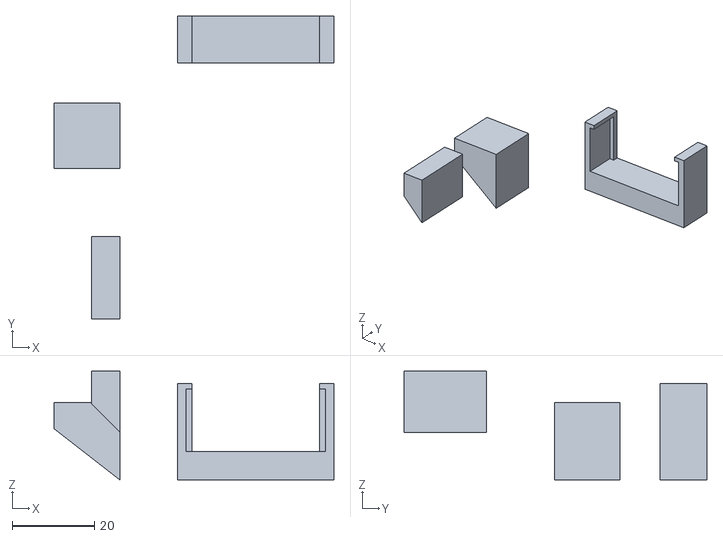
[picture p95: CAD file, 2026-10-01]
hardware/mount/_tmp/case_add.stl
68.0 x 73.6 x 26.5
