ewfefrs/pi-gaze/hardware/enclosure/out/pose/pose_bar_t20.stl

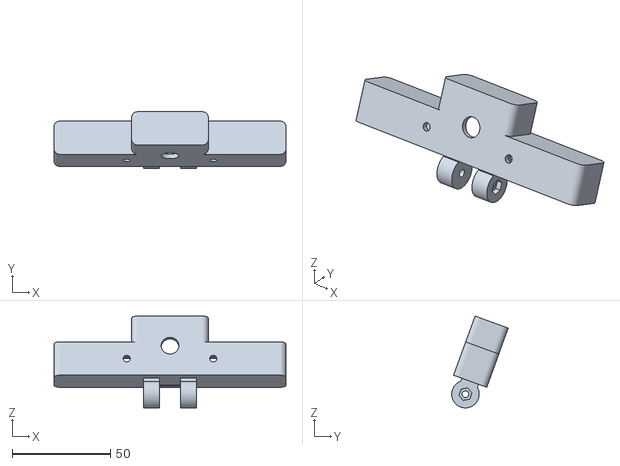
[picture p96: CAD file, 2026-10-01]
hardware/enclosure/out/pose/pose_bar_t20.stl
118.0 x 28.8 x 46.7
