ewfefrs/pi-gaze/hardware/enclosure/stl/pigaze_pad.stl

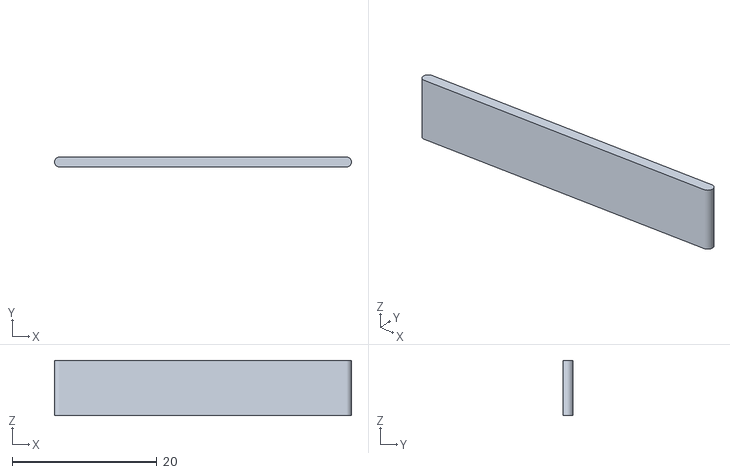
[picture p97: CAD file, 2026-10-01]
hardware/enclosure/stl/pigaze_pad.stl
41.0 x 1.40 x 7.60
