ewfefrs/pi-gaze/hardware/enclosure/out/pose/pose_barlid_t30.stl

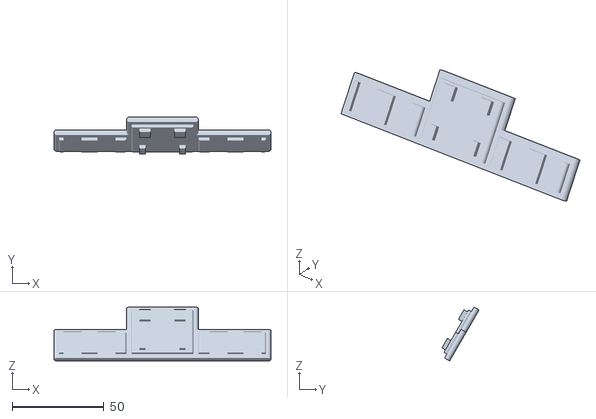
[picture p98: CAD file, 2026-10-01]
hardware/enclosure/out/pose/pose_barlid_t30.stl
118.0 x 20.2 x 29.3
