ewfefrs/pi-gaze/hardware/enclosure/stl/pigaze_bar.3mf

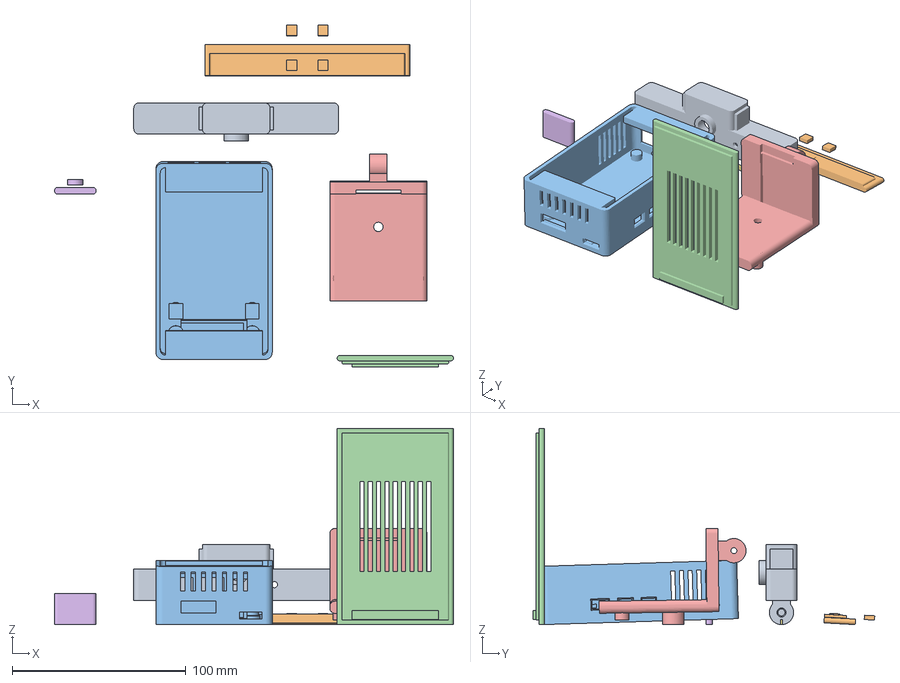
[picture p99: CAD file, 2026-10-01]
hardware/enclosure/stl/pigaze_bar.3mf
229.8 x 196.7 x 113.0 mm
pigaze_bar.stl
pigaze_bar_lid.stl
pigaze_box.stl
pigaze_box_lid.stl
pigaze_clamp.stl
pigaze_foot.stl
pigaze_pad.stl
