ewfefrs/pi-gaze/hardware/enclosure/out/pose/pose_barlid.stl

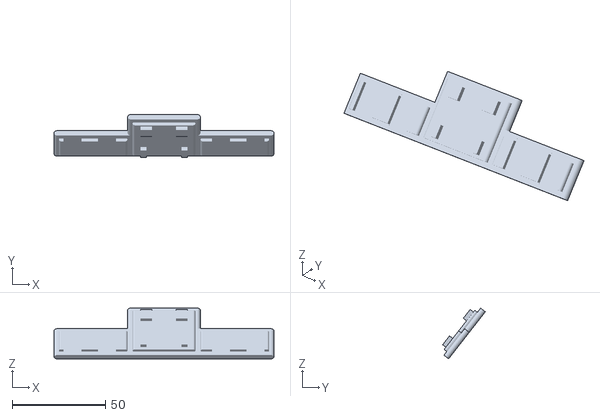
[picture p100: CAD file, 2026-10-01]
hardware/enclosure/out/pose/pose_barlid.stl
118.0 x 22.9 x 27.2
