ewfefrs/pi-gaze/hardware/enclosure/stl/pigaze_bar_lid.stl

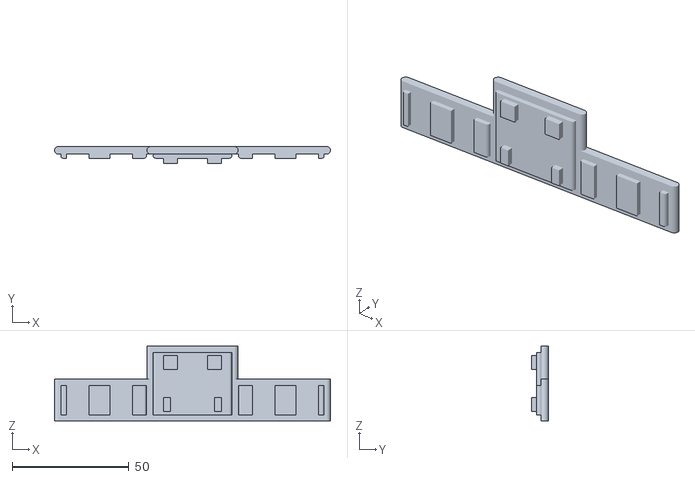
[picture p101: CAD file, 2026-10-01]
hardware/enclosure/stl/pigaze_bar_lid.stl
118.0 x 7.20 x 32.0
