ewfefrs/pi-gaze/hardware/enclosure/out/pose/pose_barlid_t20.stl

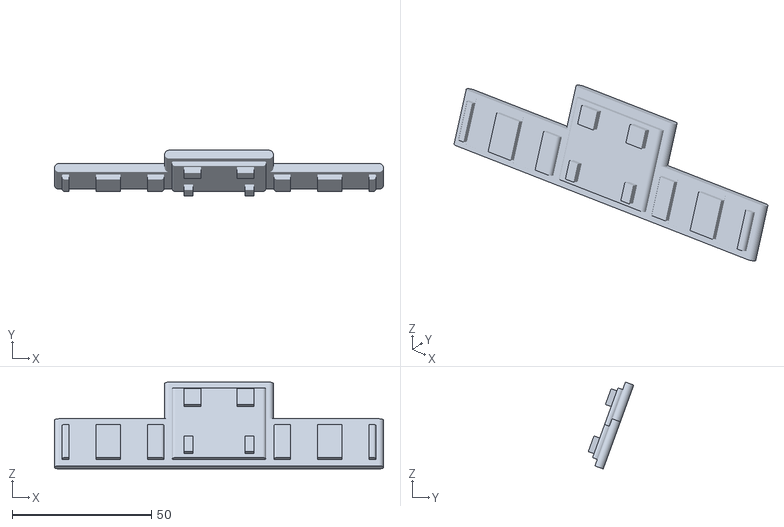
[picture p102: CAD file, 2026-10-01]
hardware/enclosure/out/pose/pose_barlid_t20.stl
118.0 x 16.3 x 31.2
