ewfefrs/pi-gaze/hardware/enclosure/stl/pigaze_ribbon_cover.stl

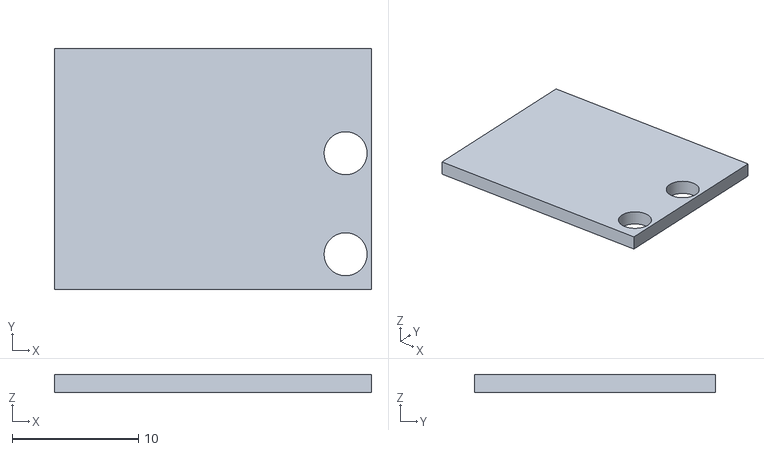
[picture p103: CAD file, 2026-10-01]
hardware/enclosure/stl/pigaze_ribbon_cover.stl
25.1 x 19.1 x 1.45
