ewfefrs/pi-gaze/hardware/enclosure/out/pose/pose_bar_t30.stl

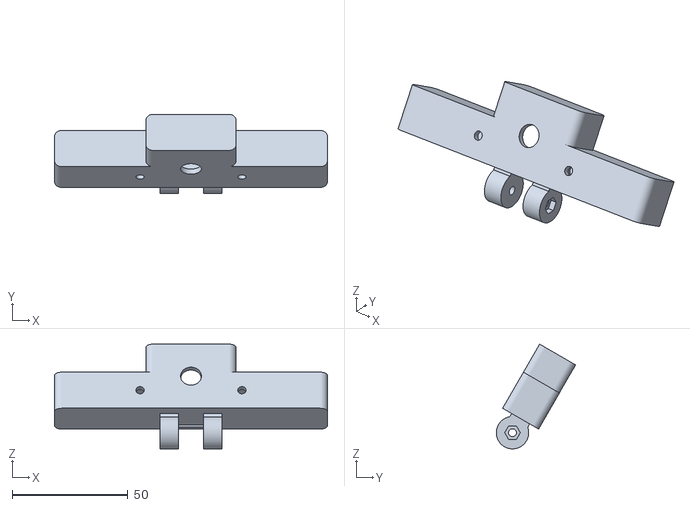
[picture p104: CAD file, 2026-10-01]
hardware/enclosure/out/pose/pose_bar_t30.stl
118.0 x 34.3 x 45.3
