ewfefrs/pi-gaze/hardware/enclosure/stl/Безымянный6.FCStd

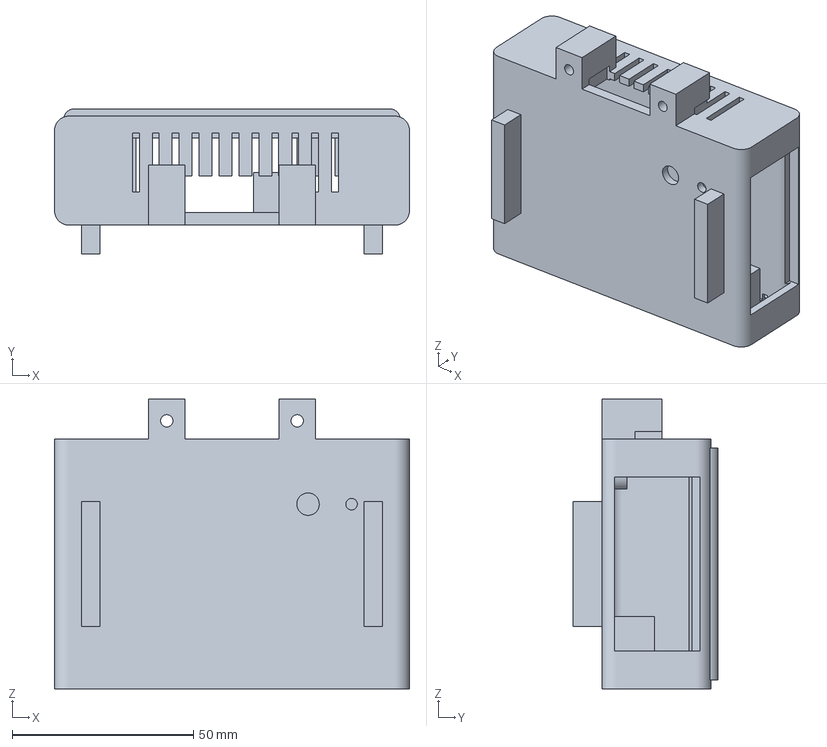
[picture p105: CAD file, 2026-10-01]
hardware/enclosure/stl/Безымянный6.FCStd
98.0 x 40.1 x 80.0 mm
