ewfefrs/pi-gaze/hardware/enclosure/stl/Безымянный7.FCStd

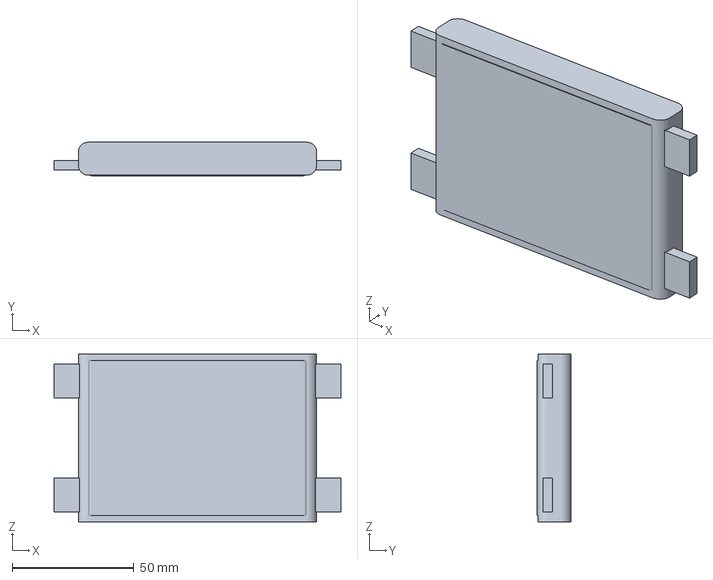
[picture p106: CAD file, 2026-10-01]
hardware/enclosure/stl/Безымянный7.FCStd
118.0 x 13.8 x 69.0 mm
