ewfefrs/pi-gaze/hardware/enclosure/out/pose/pose_bar_t38.stl

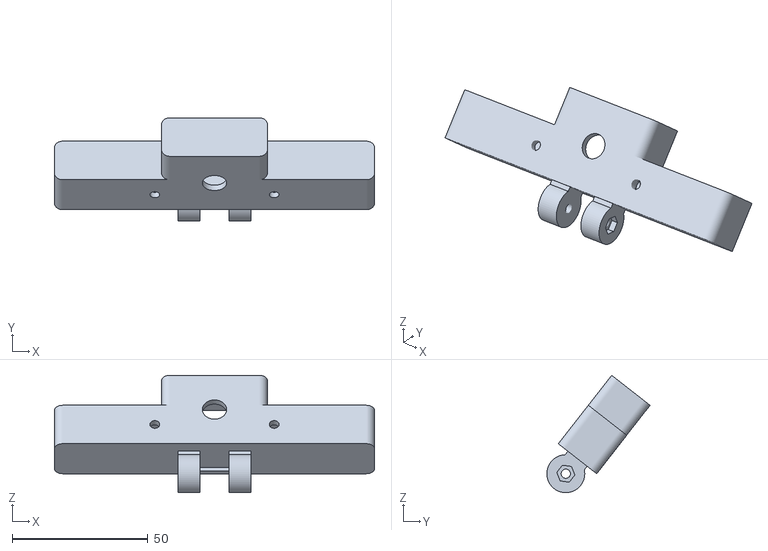
[picture p107: CAD file, 2026-10-01]
hardware/enclosure/out/pose/pose_bar_t38.stl
118.0 x 38.1 x 43.3
