ewfefrs/pi-gaze/hardware/enclosure/out/pose/pose_bar_t48.stl

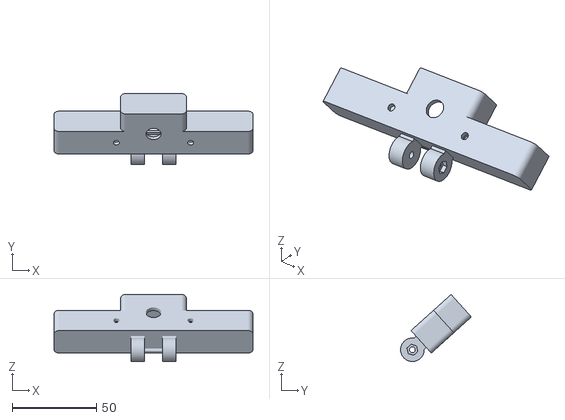
[picture p108: CAD file, 2026-10-01]
hardware/enclosure/out/pose/pose_bar_t48.stl
118.0 x 42.0 x 39.8
