ewfefrs/pi-gaze/hardware/enclosure/out/oh_bar_print.png

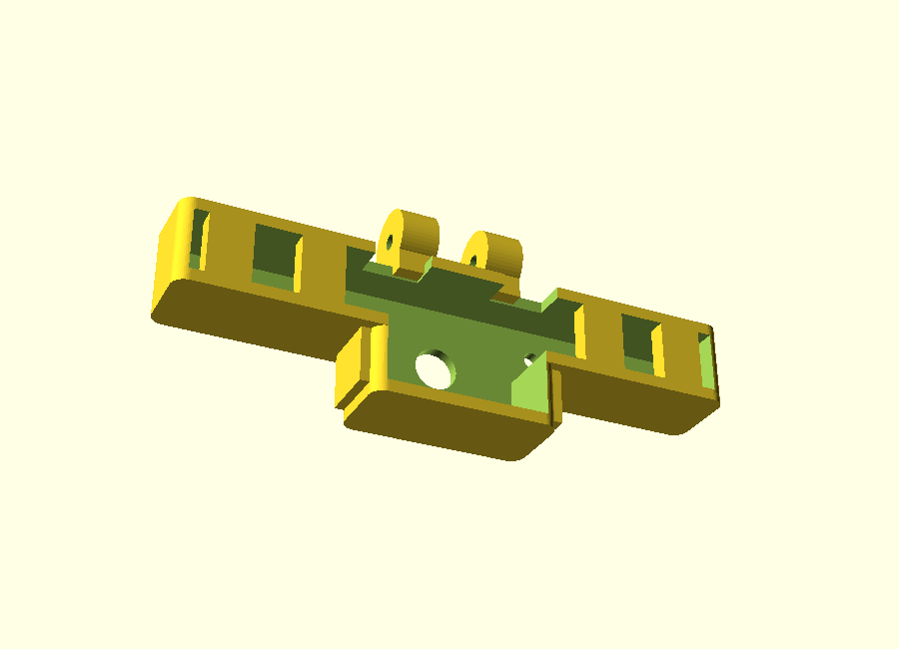
hardware/enclosure/out/oh_bar_print.png
