ewfefrs/pi-gaze/hardware/renders/assembly_preview.png

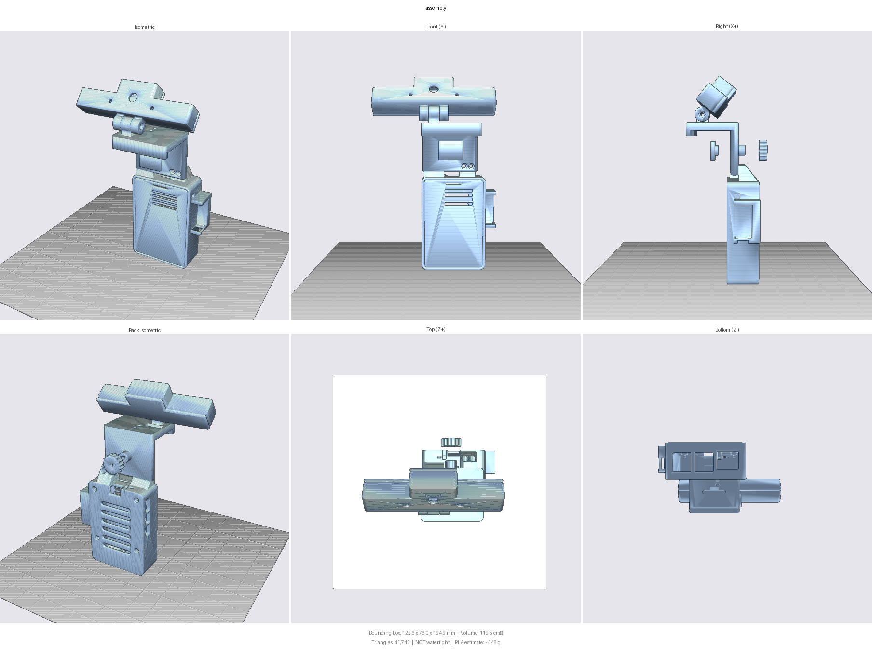
hardware/renders/assembly_preview.png
